anton-vinogradov/esp32-leshy2/drafts/legacy-2026-08-15/hardware/tscircuit/README.md

# Leshy2 — schematic as code (tscircuit)

The schematic sheets are captured as [tscircuit](https://tscircuit.com) code (`.tsx`)
transcribed from the transcribe-ready net-lists in [`hardware/`](../). From one
source file tscircuit generates the **schematic image**, a **PCB**, a **netlist**,
and a **KiCad export** — so nothing is drawn by hand.

## Sheets

| File | Sheet | Source doc |
|---|---|---|
| `power.tsx` | 1 · Power | [power.md](../power/power.md) |
| `c5-buses.tsx` | 2 · MCU + buses | [c5-buses.md](../c5-buses/c5-buses.md) |
| `rf.tsx` | 3 · RF chains | [rf.md](../rf/rf.md) |
| `audio.tsx` | 4 · Audio | [audio.md](../audio/audio.md) |
| `expansion.tsx` | 5 · Expansion (Grove-UART GPS port) | [expansion.md](../expansion/expansion.md) |
| `indicators.tsx` | 6 · Indicators / IO | [indicators.md](../indicators/indicators.md) |
| `integration.tsx` | board-level (display FPC · antenna u.FL · UI buttons · U14) | — merged, not a design sheet |

The six subsystem sheets — plus `integration.tsx` (the board-level parts that span
subsystems: the display FPC, the antenna u.FL array, the UI button block and its 3rd
PCA9555) — are **merged into one board** by `merge.py`; see below.

## Combined board — fab-drafted

All sheets are realized with **real parts**: every IC/module/connector pulls its
manufacturer-verified footprint + pinout from the LCSC/JLCPCB database
(`footprint="jlcpcb:C…"`); only mechanical/placeholder parts stay geometric.
**`board.tsx` is GENERATED** by [`merge.py`](merge.py): it strips each sheet's `<board>`
wrapper, renames the three cross-sheet refdes collisions (`U20`→`m_U20`/`rf_U20`,
`Y1`→`rf_Y1`/`a_Y1`, `Rbias`→`rf_Rbias`/`a_Rbias`), and concatenates the six sheets +
`integration.tsx` into one `<board>`. The sheets stitch by shared `net.NAME` (the whole
SPI/I²C bus, the power rails, the chip-selects, the interrupts, the C5 link, the SP4T
select). **223 components.** Never hand-edit `board.tsx` — edit a sheet (or
`integration.tsx`), then re-run `python3 merge.py`.

| File | What |
|---|---|
| `board.tsx` | **generated** — the whole device in one board (do **not** hand-edit) |
| `merge.py` | builds `board.tsx` from the 6 sheets + `integration.tsx` |
| `board-sch.svg` | whole-board schematic image |
| `board.kicad_pcb` | **KiCad PCB — the layout target (connectivity carried; not yet routed)** |

## Placement & auto-routing — drafted

From `board.kicad_pcb` an **auto-placement draft** groups the parts (a pre-integration 174-part draft) into floorplan
zones — RF up near the antenna edge, power at the bottom, MCU + buses in the centre —
with the cable/slot connectors pinned to their board edges (USB-C at the bottom,
microSD on the left, Grove on the right) and **zero courtyard overlaps**. It is
converted to a **4-layer** stack (JLC7628, `In1` = GND plane, `In2` + outer = signal)
with a real design-rule floor in the sibling `.kicad_pro`.

The digital + power nets are **auto-routed with [Freerouting](https://github.com/freerouting/freerouting)**
(board → Specctra DSN → freerouting → SES → back into KiCad via `pcbnew`), then the GND
pads are **welded to the `In1` plane** by [KiCadRoutingTools](https://github.com/drandyhaas/KiCadRoutingTools)'
plane-finalize. Result: **424 of 425 connections routed** on 4 layers — 3304 track
segments + 715 vias over a filled GND plane (0.003 Ω, ~15 A) — leaving only **one net
(the encoder B channel) + 4 DRC clearance nits**. The RF traces exist but still want an
impedance-controlled, coplanar-ground, antenna-keep-out **hand-redo in KiCad** (as RF
always does); finish those few touches → gerbers.

| File | What |
|---|---|
| `board-placed-4layer.kicad_pcb` | pre-route — 4-layer, edge-aware placement, GND-plane zone |
| `board-autorouted.kicad_pcb` | **Freerouting draft** — ~85 % routed, GND plane filled; hand-finish the rest |

> The placement is a **draft**: single-sided at ~80 × 175 mm to open routing channels;
> moving the small decoupling caps to the back shrinks it toward ~80 × 140 mm.
> Freerouting 2.x runs headless on Java 21+ (`-de in.dsn -do out.ses -mp N`); DSN/SES
> cross the KiCad boundary with `pcbnew.ExportSpecctraDSN` / `ImportSpecctraSES`.

## Render / export

Needs Node + [Bun](https://bun.sh) (the tscircuit CLI runs on Bun):

```bash
npm install                       # once — installs @tscircuit/cli locally (runs on Bun)
python3 merge.py                  # (re)generate board.tsx from the 6 sheets + integration.tsx
# Sheets use footprint="jlcpcb:C…" -> the parts engine (network) must be ON.
# Do NOT pass --disable-parts-engine, or the real footprints won't resolve.
# NOTE: give -o a RELATIVE path — the CLI mishandles a leading "/".
npx tsci export board.tsx -f kicad_pcb     -o board.kicad_pcb     # whole-board PCB (layout target)
npx tsci export board.tsx -f schematic-svg -o board-sch.svg      # whole-board schematic
# also: pcb-svg, gerbers, kicad_zip, readable-netlist, STEP, glTF …
```

**Verify connectivity** with KiCad's DRC. On the *un-placed / un-routed* merged board the
connectivity signal is **`schematic_parity` = 0** (the PCB netlist matches the schematic — no
accidental merges or breaks). Its `unconnected_items` (ratsnest) and `shorting_items` (pads of
different nets physically overlapping because nothing is placed yet) are **both artifacts of the
pre-layout board**, not real defects — they clear once parts are placed and routed:
`kicad-cli pcb drc --format json -o board.drc.json board.kicad_pcb`.

## Notes

- **Real footprints** are engine-pulled by LCSC part number (the parts engine /
  network must be on to export). Remaining **placeholders** to swap before fab: the
  18650 holder, 3.5 mm jack, electret mic, speaker, buzzer, RESET/BOOT/PTT buttons,
  the nRF24 / SA868 module lands and the CC1101 balun; LEDs are plain 0603 (pick the
  real amber part at BOM time). Each sheet's header comment lists its exact parts + `⚠`.
- **On the board now** (integration sheet): the display FPC (`J_LCD`, `LCD_*`), the
  CC1101 / UHF / Si4732 antenna u.FL connectors (`J_ANT_*`, `ANT_*`), the UI button
  block (D-pad + BACK/OPTIONS/STOP/F1/F2) and its 3rd PCA9555 (`U14`, 0x22).
- **Still off-sheet before the PCB** — intentional dangling endpoints today:
  the 7 RF envelope detectors that feed the TX-live LEDs (`TXDET_*`, Stage 3),
  the C5 USB VBUS ESD stub (`VBUS_C5`), and the module-level antennas that live on
  their own modules (the 3 nRF24 lands, the LoRa E22 IPEX).
- **RF PCB layout** (impedance-controlled feeds, ground planes, antenna
  keep-outs) is done in **KiCad** on the exported project — the auto-router is
  not used for the RF chains.
- Connectivity is by **net name** (`net.BAT`, `net.GND`, …), matching the
  "Key nets" sections of each sheet doc.
- **Schematic of record = the `.tsx` + `*-schematic.svg`** (connectivity is
  correct there). tscircuit's `kicad_sch` export currently drops the wires
  (dangling labels — fails KiCad ERC), so it is **not** committed; the
  KiCad **`.kicad_pcb`** carries the real net connectivity and is the layout
  target.

*Part of [Leshy2](../../README.md) · MIT.*
