anton-vinogradov/esp32-leshy2/drafts/project-history-2026-08-19/review/baseline.md

# Baseline перестройки документации

Дата фиксации: 2026-08-15, Europe/Moscow.

| Репозиторий | Исходный commit | Состояние до переноса |
|---|---|---|
| `esp32-leshy2` | `355ac489ba995614695874d40474fb845e7944d1` | актуальный `origin/main` перед reset |
| `esp32-leshy2-firmware` | `28e7c46710f00ab179df1b0eb488616da173688c` | актуальный `origin/main` перед reset |

Старая документация перенесена в `drafts/legacy-2026-08-15/` внутри каждого репозитория. Она сохраняет исследовательскую ценность и историю решений, но больше не является источником требований.

Старый `docsync` также архивирован: его контрольные хэши и ссылки были привязаны к прежней структуре. Новый контроль согласованности будет введён после появления первых проверенных контрактов.
