anton-vinogradov/esp32-leshy2/drafts/project-history-2026-08-19/review/reviews/REV-0005CE-current-g3-clamshell-propagation.md

# REV-0005CE — current G3 clamshell propagation

Статус: **проведено ревью geometry-reentry working projection**.

| Проверка | Результат |
|---|---|
| process entry | pass: I1…I9 working-candidate paper scopes reviewed before integrated mockup resumed |
| legacy reuse | pass: fold/mirror, board envelope, holes, inner gap and geometric checks reused without inheriting old owner/device labels |
| current locality | pass: S3+C5 UI/control half and RP RF/power half preserve electrical owners while keeping active local interfaces local |
| external inventory | pass: 3.5-inch HMX, all controls, three USB roles, storage/audio/IR, nine SMA identities, U214, Unit and exact battery family remain visible |
| drawing semantics | pass: one numbered body per shown physical device; exact/current MPN and role in one register; dashed power region is not a device |
| physical checks | pass: board bounds/overlap, SMA spacing/hole clearance, U214 overhang/gaps and complete control/antenna identity checks |
| hardware regression | pass: generator/artifact checks, 73 architecture/product tests and whitespace check |
| firmware regression | pass: 19 runtime/landing tests |
| authorization boundary | pass: G3 continues; G4 alternatives, G5 selection, G6 co-design, G7 atomic architecture and KiCad remain later gates |

## Verdict

[`G3-0001`](../product-design/G3-0001-current-clamshell-reentry.md) receives
**«Проведено ревью»** for geometry re-entry. [`FND-0117`](../findings/FND-0117-legacy-layout-was-not-a-current-g3-projection.md)
is fixed. The generated view is the current starting physical hypothesis, not
the finished product design.

Next G3 work expands the placement-critical envelope and connector/cable plane;
any physical conflict returns to its G2F owner. KiCad remains unauthorized.
