anton-vinogradov/esp32-leshy2/drafts/project-history-2026-08-19/review/reviews/REV-0005BP-bounded-principled-and-stage-diagrams.md

# REV-0005BP — bounded principled and current-stage diagrams

Статус: **проведено ревью документационных диаграмм**.

| Проверка | Результат |
|---|---|
| reproduced failure | pass: monolithic landing-page Mermaid source exceeded the GitHub text limit |
| rendered boundary | pass: first target diagram is vertical and below 12,000 source characters |
| physical identity | pass: every overview box contains one physical component, its MPN and role |
| no data loss | pass: exhaustive one-device-per-node raw projection and exact pin/net tables remain machine-generated/reviewable |
| current position | pass: gate diagram distinguishes internal `I8` inside `2F` from future top-level gate `8` |
| architecture delta | none: no component, instance, owner, pin, signal, rail or BOM quantity changed |
| regression | pass: 69/69 architecture tests, generated-artifact check and whitespace check |

## Verdict

[`FND-0113`](../findings/FND-0113-monolithic-principled-diagram-exceeded-github-limit.md)
is corrected. The start pages again provide a useful finished-product diagram,
while the exhaustive projection stays available without asking GitHub to render
an unsupported monolith.

`FND-0114/REV-0005BZ` later supersede the hidden-source presentation with a
rendered split atlas and replace the USB-led overview with owner-first maps.
The original electrical/architecture verdict remains unchanged.

I8 remains active. I9, integrated mockup and KiCad remain unauthorized.
