anton-vinogradov/esp32-leshy2/drafts/project-history-2026-08-19/review/reviews/REV-0005BZ-renderable-principled-atlas.md

# REV-0005BZ — renderable principled-device atlas

Статус: **проведено ревью документационных диаграмм**.

| Проверка | Результат |
|---|---|
| landing-page entry | pass: architecture starts from S3/C5/RP ownership, not USB |
| readable slices | pass: separate S3, C5, RP and power diagrams in both target README files |
| exhaustive projection | pass: all 858 current physical instances are emitted; 44 PD/charger support positions missing from the old raw view were restored |
| Mermaid boundary | pass: 25 detailed blocks; largest block remains below the 12,000-character limit |
| physical identity | pass: one physical instance per node with exact/current MPN and role; explicit `MPN TBD` remains visible |
| raw preservation | pass: full monolithic `.mmd` is generated as a machine-review artifact |
| synchronization | pass: generator rewrites and checks both target README sections together with the detailed atlas |
| architecture delta | none: no device, quantity, owner, pin, signal, rail, power policy or BOM value changed |
| regression | pass: generated-artifact check, architecture suite and whitespace check |

## Verdict

[`FND-0114`](../findings/FND-0114-hidden-projection-and-usb-led-overview.md)
получает статус **«Исправлено»**. Диаграммный шаг получает статус
**«Проведено ревью»**: landing page объясняет архитектуру от владельцев, а
полная начинка действительно рендерится несколькими ограниченными схемами.

I8, I9, integrated mockup и KiCad не продвигаются этим документационным
изменением.
