anton-vinogradov/esp32-leshy2/drafts/project-history-2026-08-19/review/reviews/REV-0004L-digital-noninterference-layout.md

# REV-0004L — digital non-interference layout

> Subsequent amendment: `DEC-0059/REV-0005L` replaces the reviewed 4-bit
> S3↔C5 pin group with dedicated 1-bit SDIO plus full S3/C5 service. Current
> machine evidence is in `NIF-0001` and the generated atlas.

- Статус: **Проведено ревью исходной компоновки; current budget повторно проверен `REV-0004V`**
- Дата: 2026-08-17
- Decision: [`DEC-0044`](../decisions/DEC-0044-delegated-noninterference-layout.md)
- Artifact: [`NIF-0001`](../architecture/NIF-0001-digital-noninterference-layout.md)
- Machine source: [`G2F-3I`](../../../hardware/architecture/candidates/G2F-3I.json)

## Проверки

| Проверка | Результат |
|---|---|
| exact S3/C5 module and RP2354B QFN80 contacts exist | pass |
| every programmable exposed GPIO is used/reserved/free exactly once | current pass after `DEC-0046`: S3 `29/3/4`, C5 `14/6/1`, RP `48/0/0`; corrected by `FND-0059/REV-0004V` |
| every TCA6424 allocatable contact classified | historical pass: `23/1/0`; subsequent audio/CC reviews produced main `23/0/1`; post-DEC-0098 current projection is main `24/0/0` plus UI `7/1/0` |
| duplicate JSON keys fail before semantic validation | pass |
| every strap allocation has explicit reset proof | pass |
| every programmable peer link reciprocates the same net | pass |
| each domain has independent programming/recovery/diagnostics | pass on contacts: S3 USB, C5 UART0+EN/BOOT/strap, RP USB+SWD+RUN+BOOTSEL |
| RP2354B PIO data pins obey the real shared base window | pass: PIO0 and PIO1 select `GPIO16…GPIO47`; all PIO data are `GPIO30…GPIO46` |
| fixed-function mux contacts match exact-device groups | pass: S3 USB, C5 4-bit SDIO, RP SPI1/UART0/UART1/I²C0 contracts |
| RP PIO state-machine capacity | pass: `5/12`, seven reserve |
| RP DMA worst-case persistent capacity | pass: `13/16`, three reserve |
| S3 directional GDMA capacity | pass: TX `3/5`, RX `3/5`; two reserve in each direction |
| 3×nRF24, CC1101 and U214 share a data bus | no; five physical buses/state machines |
| C5 IPC shares controller with microSD | no; C5 exclusively uses S3 SD/MMC host |
| RP IPC shares controller with display/storage | no; dedicated SPI3/SPI1 |
| remaining scheduled resources declare arbiter/deadline/proof gate | pass: display+SD and internal slow I²C only |
| generator tests | historical pass: 19 tests; current suite is rerun and reported by the newest review artifact |

## Найдено и исправлено в ходе перебора

| Несоответствие | Исправление |
|---|---|
| RP2354A forced four compatibility radios onto one 10 Mbit/s bus | RP2354B/QFN80 and four independent PIO0 buses |
| first B-package map put C5 and microSD on one S3 host | microSD moved to SPI2; C5 gets exclusive 4-bit SDIO |
| proposed RP UART gave only 1.6 MB/s raw against ≥1.5 MB/s framed gate | rejected; RP returns to dedicated 20 MHz SPI |
| proposed C5 UART ignored exact 5 Mbit/s device limit | rejected using official ESP-IDF SoC capability |
| first RP2354B pin map crossed the physical PIO GPIO-base window | all five PIO data groups moved into `GPIO16…GPIO47`; CS/CE/IRQ remain direct GPIO; machine regression added |
| 16-port slow plane did not cover 19…27 demand | accepted 24-port envelope; 23 endpoints routed, one reserve |
| old validator could not detect duplicate JSON keys or service alternatives | parser/validator and regression tests extended |
| post-review quiet-state controls made the displayed C5/RP budget stale | counts regenerated and protected by focused pinout artifact/test in `FND-0059/REV-0004V` |

## Review boundary

Статус относится к **бумажной цифровой компоновке и её machine checks**, а не
к complete target architecture. Physical RF coexistence, electrical signal
integrity, exact peripheral MPNs, power, mechanics, cost and HIL remain open.
Следующий шаг — RF self-desense/coexistence proof; неизбежную взаимную
деградацию нельзя закрыть этим ревью.
