anton-vinogradov/esp32-leshy2/drafts/project-history-2026-08-19/review/reviews/REV-0005AO-display-endpoint-propagation.md

# REV-0005AO — display endpoint propagation review

> Subsequent `REV-0005AQ` changes TP_INT routing and consumes GPIO39/47 for the
> encoder; the display endpoint reviewed here otherwise remains unchanged.

- Status: **Проведено ревью**
- Decision: [`DEC-0084`](../decisions/DEC-0084-exact-protected-display-electrical-endpoint.md)
- Finding: [`FND-0088`](../findings/FND-0088-display-endpoint-still-contained-abstract-circuits.md)

## Propagation checked

| Consumer | Result |
|---|---|
| machine device registry | exact connector, switch and two new resistor MPNs expose every real contact |
| G2F-3I instances/routes | connector separates board and panel; logic/backlight/reset/fault routes are exact; no GPIO added |
| allocation regression | S3 remains `32 used / 3 reserved / 1 free`; GPIO40 now ends on the exact PWM gate circuit |
| product diagram | every added physical component is a separate vertical-diagram node with MPN and role |
| display register/fit docs | prior exact 40-contact fit is amended by the protected electrical endpoint while procurement/mate evidence stays open |
| firmware contract | reset waits, default-off backlight, latch behavior, no auto-retry and HIL-only connector maturity are explicit |
| stage state | I4 remains active; only the display paper electrical endpoint receives «Проведено ревью» |

## Review boundary

The checked JSON and generated atlas agree, and the paper circuit has no
abstract display supply/backlight endpoint. This review does not authorize
KiCad, connector footprint freeze, panel purchase as a production MPN or any
mechanical mockup update.
