anton-vinogradov/esp32-leshy2/drafts/project-history-2026-08-19/review/reviews/REV-0005V-2s-manager-decision-propagation.md

# REV-0005V — 2S manager decision propagation

- Статус: **Проведено ревью**
- Дата: 2026-08-18
- Decision: [`DEC-0066`](../decisions/DEC-0066-max17320-mspm0-fail-closed-manager.md)
- Device review: [`PWR-0005`](../architecture/PWR-0005-replaceable-2s-manager-options.md)

## Review result

| Check | Result |
|---|---|
| owner choice | pass: option A accepted exactly as `MAX17320G20+T + MSPM0C1104SDGS20R` |
| real devices | pass: current ADI/TI order codes, lifecycle, package and all exposed contacts are machine-recorded |
| no hidden authentication | pass: exact G20 has no SHA-256; no secret or irreversible lock is required |
| startup safety | pass at architecture level: protected gauge image/readback is a production interlock; ALRT hold remains asserted across blank/reset/watchdog admission MCU states |
| service/recovery | pass at boundary: gauge I2C/NVM/hold/fault and MCU NRST/SWD/UART/VDD/VSS have direct fixture access |
| MCU GPIO budget | pass: 10 used, 5 reserved, 3 free across all 18 real DGS20 GPIO-capable contacts |
| MCU power claim | pass with explicit boundary: AOLDO is only for measured low-clock operation; programming/recovery uses an isolated external source |
| system integration | pass: dedicated local gauge bus; bounded shared system I2C/IRQ; no radio/display/storage controller dependency |
| target diagrams | pass: EN/RU and generated vertical diagrams show the two exact physical devices separately with roles |
| firmware projection | pass: local admission ownership and fourth independently recoverable image domain are propagated; S3 cannot override refusal |
| downstream electrical work | open but bounded: exact FET/fuse/NTC/shunt/load/hold/supply-isolation and HIL are named |
| CAD boundary | pass: no KiCad authorization implied |

## Conclusion

The exact manager decision, contacts, resources, recovery and cross-repository
projection receive **«Проведено ревью»**. `I3` advances to the complete
MAX17320 surrounding circuit and loss/fault calculations.
