anton-vinogradov/esp32-leshy2/drafts/project-history-2026-08-19/review/improvements/IMP-0053-5v-typec-versus-pd-charge-path.md

# IMP-0053 — 5-V Type-C power path versus USB-PD

- Статус: **Принято B; закрыто DEC-0063/REV-0005R**
- Дата: 2026-08-18
- Context: [`PWR-0003`](../architecture/PWR-0003-charge-power-path-options.md)
- Battery behavior: [`DEC-0062`](../decisions/DEC-0062-individually-replaceable-2s-cells.md)
- Decision: [`DEC-0063`](../decisions/DEC-0063-sink-only-30w-usb-pd-power-path.md)

## Decision options

- **A / `C5V` — recommended:** ordinary 5-V Type-C/legacy input with explicit
  source-current detection, 2S NVDC boost charger/power path and separate real
  gauge/protector. Lowest complete BOM and complexity; charging is load-aware
  and may slow/pause during high-power use.
- **B / `CPD`:** USB-C PD controller plus wide-input 1–4S buck-boost charger.
  Faster/more headroom, but adds cost, area, PD image/provisioning, compliance
  and high-voltage fault work without a current product requirement.
- **C / `CLEG`:** repair the old BQ25887 design with external missing blocks.
  Rejected as dominated after its apparent part-count advantage disappears.

## Historical recommendation and owner decision

Accept **A / C5V**. It preserves ordinary charger compatibility, USB-only
recovery and battery supplement without paying for unrequested fast charging.

After the owner requested the installed-cost delta, the complete comparison
showed approximately USD 2–3/device at the visible 100-piece tier rather than
an order-of-magnitude penalty. The owner explicitly selected **B / CPD** and
bounded it to sink-only 30 W. `DEC-0063/PWR-0004` supersede the historical
recommendation and add the mandatory EEPROM/provisioning/recovery details.
