anton-vinogradov/esp32-leshy2/drafts/project-history-2026-08-19/review/reviews/REV-0005N-target-product-site-cleanup.md

# REV-0005N — target product-site cleanup

- Статус: **Проведено ревью**
- Дата: 2026-08-17
- Decision: [`DEC-0060`](../decisions/DEC-0060-github-target-product-site.md)
- Finding: [`FND-0072`](../findings/FND-0072-target-readmes-contained-engineering-chronology.md)

## Проверено

| Проверка | Результат |
|---|---|
| hardware EN/RU landing | product purpose, capabilities, physical design, safety and docs navigation retained |
| firmware EN/RU landing | product behavior, UI, radio services, data, STOP, update/recovery and docs navigation retained |
| review chronology | `DEC/REV/FND/IMP` chains removed from all four target pages |
| maturity | detailed progress remains in both `docs/status/current-state.*.md` pairs |
| traceability | review ledger and current-state links remain visible at top/bottom |
| hardware diagram | vertical `flowchart TD`, exact MPN coverage and one-device-per-node projection retained |
| pin mapping | exact groups retained in responsive `<details>` list; generated atlas remains linked |
| firmware visualization | vertical safe-session state flow added in both languages |
| product scope | no accepted capability, exclusion or safety guarantee removed |
| regression | hardware architecture suite **41/41 pass**; firmware target-page suite **2/2 pass** |

## Boundary

Этот review подтверждает качество entrypoints и сохранение принятого product
scope. Он не повышает зрелость electronics/firmware implementation и не закрывает
никакие текущие component, power, RF, HIL или `INT-0001/I2` decisions.
