anton-vinogradov/esp32-leshy2/drafts/project-history-2026-08-19/review/reviews/REV-0005J-internals-before-integrated-mockup.md

# REV-0005J — internals before integrated mockup propagation review

- Статус: **Проведено ревью процесса; subsequent `DEC-0059/REV-0005L` закрывают I1 и активируют I2**
- Дата: 2026-08-17
- Decision: [`DEC-0058`](../decisions/DEC-0058-internals-before-integrated-mockup.md)
- Sequence: [`INT-0001`](../architecture/INT-0001-internal-design-closure-sequence.md)

## Проверенный результат

| Gate | Результат |
|---|---|
| owner instruction | pass: integrated mockup resumes only after internal-design closure |
| existing U214 proof | retained: `PHY-0001/DEC-0057` remains a bounded envelope decision, not continued industrial design |
| process cycle | pass: project-level electrical closure is separated from prototype/enclosure-only HIL |
| physical work boundary | pass: local part/connector/thermal/RF fit checks remain allowed only as internal feasibility inputs |
| dependency order | pass: `INT-0001/I0…I9` covers compute, safety, power, UI, audio, RF, expansion, BOM and whole-internal review |
| next prerequisite | pass: compute/recovery/service is first; `FND-0070/IMP-0049` exposes rather than hides the SDIO collision |
| target behavior | no delta: product capability and three safety levels do not change |
| firmware repository | historical at this review; `DEC-0059` later creates the transport delta |

## Conclusion

The previous wording that the next pass starts integrated G3 mockup is
superseded. Current work stays in internal feasibility/closure until `I9`;
mockup and industrial layout remain paused, while KiCad is still blocked.
