anton-vinogradov/esp32-leshy2/drafts/project-history-2026-08-19/review/audits/AUD-0004-current-competitor-capability-gap.md

# AUD-0004 — current competitor capability and product-design gap

- Статус: **Проведено ревью; `W-EXTRA-11..17` закрыты**
- Дата snapshot: 2026-08-16
- Finding: [`FND-0040`](../findings/FND-0040-current-competitor-benchmark-missing.md)
- Scope: official product/project documentation; shipping and prototype states
  are never merged

## Representative products

| Product/class | Current official facts relevant to Leshy2 | Design lesson, not copied solution |
|---|---|---|
| Flipper Zero, shipping compact multi-tool | 100×40×25 mm, 102 g, 2100 mAh, 1.4-inch sunlight-readable 128×64 LCD, D-pad/back, microSD, USB-C, CC1101, LF RFID, NFC, IR, BLE/802.15.4, iButton and GPIO; claimed battery life up to 28 days | pocket control can remain complete without touch/keyboard; field runtime/readability, lanyard and contact tools are product-level requirements |
| M5 Cardputer-Adv, shipping card terminal | 84×54×19.6 mm, 81 g, 1750 mAh, 56-key keyboard, 240×135 display, ES8311/mic/speaker/jack, IR TX, microSD, Grove and 14-pin expansion, lanyard; U214 Cap adds LoRa+GNSS | keyboard and cap mechanics are viable in a small device, but screen area and antenna/accessory volume are constrained |
| LILYGO T-Deck Plus, shipping dev platform | 100×68×11 mm, 2.8-inch 320×240, keyboard+trackball, 2000 mAh, microSD, LoRa and GNSS; no touch; Plus consumes its Grove pins for GNSS | large landscape face improves UI/text, while fixed onboard radios can remove general expansion and force bus sharing |
| LILYGO T-Embed CC1101, shipping integrated dev platform | 97.5×39×31 mm, 1.9-inch 320×170, encoder, CC1101, PN532, IR, mic/speaker, TF, 1300 mAh and two QWIIC ports | narrow one-hand/encoder shell can carry many blocks, but thickness, controls and RF/antenna honesty need explicit review |
| ESP32 Marauder, active open project | hardware variants deliberately span 2.8-inch touch, 1.44-inch 5-way compact control, SD/battery/GPS and CLI; current feature matrix includes Wi-Fi/BLE analysis, raw capture and PMKID | one firmware does not prove one optimal enclosure; control/display profiles are real product variants |
| Flipper One, **prototype not for sale** | preliminary 155×67×40 mm, 22.9 Wh, Linux RK3576 + low-power RP2350, 256×144 grayscale display, D-pad/touchpad/PTT, USB host/PD, Wi-Fi 6E 2.4/5/6, M.2 and modular antenna rail | high-speed/Linux/extensible class is physically and economically different; its provisional features are competitor direction, not a baseline fact to clone |
| HackRF One, shipping SDR peripheral | open 1 MHz–6 GHz half-duplex, 20 Msps 8-bit IQ, high-speed USB, no autonomous UI/battery | wideband SDR requires a different RF/compute/data/power class; external/deferred disposition is honest unless the whole product class changes |

## Sources

- [Flipper Zero official product/specifications](https://flipper.net/)
- [Flipper Zero iButton](https://docs.flipper.net/zero/ibutton) and
  [U2F](https://docs.flipper.net/zero/u2f) documentation
- [Flipper One preliminary technical specifications](https://docs.flipper.net/one/general/tech-specs),
  [Wi-Fi/Bluetooth](https://docs.flipper.net/one/hardware/wifi-bluetooth) and
  [module mounting](https://docs.flipper.net/one/mechanics/module-mounting-system)
- [M5Stack Cardputer-Adv](https://docs.m5stack.com/en/core/Cardputer-Adv) and
  [Cardputer Mesh Kit/U214](https://docs.m5stack.com/en/core/Cardputer_Mesh_Kit)
- [LILYGO T-Deck Plus](https://wiki.lilygo.cc/products/t-deck-series/t-deck-plus/)
- [LILYGO T-Embed CC1101](https://wiki.lilygo.cc/products/t-embed-series/t-embed-cc1101/)
- [ESP32 Marauder current hardware matrix](https://github.com/justcallmekoko/ESP32Marauder/wiki/marauder-versions)
- [Great Scott Gadgets HackRF One](https://greatscottgadgets.com/hackrf/one/)
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
