anton-vinogradov/esp32-leshy2/drafts/project-history-2026-08-19/review/decisions/DEC-0058-internals-before-integrated-mockup.md

# DEC-0058 — finish the internal design before resuming the integrated mockup

- Статус: **Принято владельцем; проведено ревью propagation**
- Дата: 2026-08-17
- Основание: прямое указание владельца продолжать mockup только после полного
  завершения работ над начинкой
- Closure sequence: [`INT-0001`](../architecture/INT-0001-internal-design-closure-sequence.md)
- Review: [`REV-0005J`](../reviews/REV-0005J-internals-before-integrated-mockup.md)
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
