anton-vinogradov/esp32-leshy2/hardware/product-design/g3_clamshell.py

#!/usr/bin/env python3
"""Generate and validate dimensioned Leshy2 mechanical projections."""

from __future__ import annotations

import argparse
import html
import json
import math
import xml.etree.ElementTree as ET
from dataclasses import dataclass
from pathlib import Path


REPO = Path(__file__).resolve().parents[2]
DEVICES_PATH = REPO / "hardware/architecture/devices.json"
CANDIDATE_PATH = REPO / "hardware/architecture/candidates/G2F-3I.json"
MECHANICAL_GATES_PATH = REPO / "hardware/product-design/mechanical-evidence-gates.json"
SOURCE_RESEARCH_PATH = REPO / "hardware/product-design/h1-source-research.json"
NAVIGATION_CLUSTER_PATH = REPO / "hardware/product-design/navigation-cluster.json"
DISPLAY_MOUNT_DESIGN_PATH = REPO / "hardware/product-design/display-mount.json"
ASSEMBLY_COORDINATE_MODEL_PATH = REPO / "hardware/product-design/assembly-coordinate-model.json"
H1_R2_PLACEMENT_PATH = REPO / "hardware/product-design/h1-r2-placement.json"
EXTERNAL_OUTPUT = REPO / "docs/images/current-clamshell.svg"
SERVICE_OUTPUT = REPO / "docs/images/service-access.svg"
INTERNAL_OUTPUT = REPO / "docs/images/internal-board-layout.svg"
SANDWICH_OUTPUT = REPO / "docs/images/sandwich-section.svg"
TOP_EDGE_OUTPUT = REPO / "docs/images/top-edge-view.svg"
NAVIGATION_OUTPUT = REPO / "docs/images/navigation-cluster.svg"
DISPLAY_MOUNT_OUTPUT = REPO / "docs/images/display-mount.svg"
SOURCE_TABLE_OUTPUT = REPO / "hardware/product-design/generated/H1-physical-source-table.json"
SOURCE_REGISTER_OUTPUT = REPO / "docs/physical-source-register.md"
UNIFIED_COORDINATE_TABLE_OUTPUT = REPO / "hardware/product-design/generated/H1-unified-coordinate-table.json"
EXTERNAL_ACCEPTANCE_OUTPUT = REPO / "hardware/product-design/generated/H1-external-face-acceptance.json"
CROSS_VIEW_ACCEPTANCE_OUTPUT = REPO / "hardware/product-design/generated/H1-cross-view-acceptance.json"

BOARD_W = 80.0
BOARD_H = 150.0
DISPLAY_Y = 10.5
DISPLAY_W = 56.54
DISPLAY_H = 84.96
DISPLAY_X = (BOARD_W - DISPLAY_W) / 2
MOUNT_HOLE_D = 2.7
MOUNT_KEEPOUT_R = 4.0
HOLES = ((5.0, 11.0), (BOARD_W - 5.0, 11.0), (5.0, 145.0), (BOARD_W - 5.0, 145.0))

INTERBOARD_GAP_MM = 11.0
MIN_INTERBOARD_Z_CLEARANCE_MM = 0.7
INTENTIONAL_INTERBOARD_MATES = {
    ("m1_ui_plug", "m1_rf_receptacle"),
}

U214_X = (BOARD_W - 84.0) / 2
U214_Y = 17.02
U214_W = 84.0
U214_H = 24.0
U214_CLEARANCE = 0.7
U214_CONNECTOR_W = 17.78
U214_CONNECTOR_D = 5.08
U214_CONNECTOR_PTH_KEEPOUT_W = 17.78
U214_CONNECTOR_PTH_KEEPOUT_D = 3.81
U214_CONNECTOR_X = (BOARD_W - U214_CONNECTOR_W) / 2
# The U214 male Cap-Bus exits normal to its broad rear face.  The exact host
# socket is therefore vertical on the raised Cardputer-like rear rail and is
# projected beneath the installed Cap envelope, not beside it.
U214_CONNECTOR_Y = U214_Y + (U214_H - U214_CONNECTOR_D) / 2
U214_RETENTION_PITCH = 56.0
U214_RETENTION_X = (
    U214_X + (U214_W - U214_RETENTION_PITCH) / 2,
    U214_X + (U214_W + U214_RETENTION_PITCH) / 2,
)
U214_RETENTION_Y = U214_Y + U214_H / 2
PACK_HOLDER_Y = 42.0
PACK_HOLDER_H = 86.0
PACK_CELL_Y = PACK_HOLDER_Y + 10.0
PACK_HOLDER_BODY_W = 39.78
PACK_HOLDER_BODY_H = 77.06
PACK_HOLDER_X_OFFSET = 0.0
PACK_HOLDER_CENTRE_X = BOARD_W / 2
PACK_HOLDER_PAD_X = PACK_HOLDER_CENTRE_X - 39.8 / 2
PACK_HOLDER_DRAWING_X = PACK_HOLDER_PAD_X
PACK_HOLDER_BODY_X = PACK_HOLDER_CENTRE_X - PACK_HOLDER_BODY_W / 2
PACK_CELL_CENTRES_X = (PACK_HOLDER_CENTRE_X - 9.55, PACK_HOLDER_CENTRE_X + 9.55)
PACK_HOLDER_BODY_Y = PACK_HOLDER_Y + (PACK_HOLDER_H - PACK_HOLDER_BODY_H) / 2

# Exact GCT RFPC-SMA31/SMA32 1.6-mm edge-launch family. The 10.2-mm
# plan width includes the nut envelope; the 6-mm board-side depth comes from
# the exact land/body drawing rather than the full external threaded length.
RF_BODY_W = 10.2
RF_BODY_D = 6.0
RF_BARREL_D = 6.35
RF_BARREL_OUT = 11.4
FRONT_RF = (
    (10.6, "N24-0", "SMA"),
    (25.3, "S3-2G4", "RP-SMA"),
    (40.0, "N24-1", "SMA"),
    (54.7, "C5-2G4/5", "RP-SMA"),
    (69.4, "N24-2", "SMA"),
)
REAR_RF = (
    # Five 10.2-mm SMA bodies use equal 14.7-mm pitch.
    (10.6, "RX-FM/SW", "SMA"),
    (25.3, "RX-AM/LW", "SMA"),
    (40.0, "CC-SUB", "SMA"),
    (54.7, "VOICE-VHF", "SMA"),
    (69.4, "VOICE-UHF", "SMA"),
)
VOICE_V_RF_CORRIDOR = ((54.7, 0.0), (20.25, 32.52))
VOICE_U_RF_CORRIDOR = (
    (69.4, 0.0),
    (69.4, 6.0),
    (66.5, 6.0),
    (66.5, 30.0),
    (71.2, 36.95),
)
OPPOSITE_FACE_CLEARANCE_MM = 1.5

# H1-R2.39 fail-closed placement scope. These are the already accepted G2F-3I
# Cap-Bus protection/control and hardware TX-evidence aggregate bodies. The
# values bind each instance to its current exact device key: a substitution,
# omitted coordinate or duplicate projection must fail generation.
CAP_EVIDENCE_COORDINATE_INSTANCE_DEVICES = {
    "u214_connector": "samtec_hle_107_02_g_dv_pe_lc",
    "u214_i2c_iso": "tca4307dgkr",
    "u214_i2c_iso_bypass": "yageo_cc0402krx7r9bb104",
    "u214_i2c_host_sda_pullup": "uniroyal_0402wgf2201tce",
    "u214_i2c_host_scl_pullup": "uniroyal_0402wgf2201tce",
    "u214_host_buffer_a": "nexperia_74lvc126apw_118",
    "u214_host_buffer_b": "nexperia_74lvc126apw_118",
    "u214_return_buffer": "nexperia_74lvc126apw_118",
    "u214_host_buffer_a_bypass": "yageo_cc0402krx7r9bb104",
    "u214_host_buffer_b_bypass": "yageo_cc0402krx7r9bb104",
    "u214_return_buffer_bypass": "yageo_cc0402krx7r9bb104",
    "u214_series_rst": "panasonic_erj_2rkf22r0x",
    "u214_series_gps_rx": "panasonic_erj_2rkf22r0x",
    "u214_series_sck": "panasonic_erj_2rkf22r0x",
    "u214_series_mosi": "panasonic_erj_2rkf22r0x",
    "u214_series_nss": "panasonic_erj_2rkf22r0x",
    "u214_series_busy": "panasonic_erj_2rkf22r0x",
    "u214_series_irq": "panasonic_erj_2rkf22r0x",
    "u214_series_gps_tx": "panasonic_erj_2rkf22r0x",
    "u214_series_miso": "panasonic_erj_2rkf22r0x",
    "u214_esd_a": "ti_tpd4e05u06_dqar",
    "u214_esd_b": "ti_tpd4e05u06_dqar",
    "u214_esd_c": "ti_tpd4e05u06_dqar",
    "u214_req_pulldown": "yageo_rc0402fr_0710kl",
    "u214_supervisor": "ti_tps3808g33_dbvr",
    "u214_supervisor_bypass": "yageo_cc0402krx7r9bb104",
    "u214_supervisor_sense_top": "yageo_rc0402fr_07110kl",
    "u214_supervisor_sense_bottom": "yageo_rc0402fr_07220kl",
    "u214_supervisor_ct": "murata_grm155r71h103ka88d",
    "u214_supervisor_pullup": "yageo_rc0402fr_0710kl",
    "any_tx_aon_pullup": "yageo_rc0402fr_0710kl",
    "evidence_or_0": "onsemi_bat54alt1g",
    "evidence_or_1": "onsemi_bat54alt1g",
    "evidence_or_2": "onsemi_bat54alt1g",
    "evidence_or_3": "onsemi_bat54alt1g",
    "evidence_or_4": "onsemi_bat54alt1g",
    "evidence_main_isolator": "ti_sn74lvc3g07_dcur",
    "evidence_main_isolator_bypass": "yageo_cc0402krx7r9bb104",
    "ext_evidence_buffer": "ti_sn74lvc1g07_dckr",
    "ext_evidence_buffer_bypass": "yageo_cc0402krx7r9bb104",
    "ext_evidence_input_pullup": "yageo_rc0402fr_0710kl",
    "ext_evidence_input_series": "yageo_rc0402fr_071kl",
    "ext_evidence_output_pullup": "yageo_rc0402fr_0710kl",
}
CAP_EVIDENCE_COURTYARD_HALO_MM = 0.35
RF_INSTANCE_BY_PATH = {
    "S3-2G4": "s3_external_rp_sma",
    "C5-2G4/5": "c5_external_rp_sma",
    "RX-FM/SW": "receiver_fmsw_external_sma",
    "RX-AM/LW": "receiver_amlw_external_sma",
    "N24-0": "nrf0_external_sma",
    "CC-SUB": "cc_external_sma",
    "N24-1": "nrf1_external_sma",
    "VOICE-VHF": "voice_v_external_sma",
    "VOICE-UHF": "voice_external_sma",
    "N24-2": "nrf2_external_sma",
}
RF_SOURCE_INSTANCE_BY_PATH = {
    "S3-2G4": "s3",
    "C5-2G4/5": "c5",
    "RX-FM/SW": "receiver",
    "RX-AM/LW": "receiver",
    "N24-0": "nrf0",
    "CC-SUB": "cc",
    "N24-1": "nrf1",
    "VOICE-VHF": "voice_v",
    "VOICE-UHF": "voice",
    "N24-2": "nrf2",
}
BOARD_RF_CABLE_TO_TRACE_HANDOFFS = frozenset(
    {
        "s3_rf_board_connector",
        "c5_rf_board_connector",
        "nrf0_rf_board_connector",
        "nrf1_rf_board_connector",
        "nrf2_rf_board_connector",
    }
)
RF_USER_LABEL_LINES = {
    "S3-2G4": ("WI-FI/BLE", "2.4 GHz"),
    "C5-2G4/5": ("WI-FI/15.4", "2.4/5 GHz"),
    "RX-FM/SW": ("FM/SW", "AIR RX"),
    "RX-AM/LW": ("AM/LW LOOP",),
    "N24-0": ("nRF1", "2.4 GHz"),
    "CC-SUB": ("SUB-GHz",),
    "N24-1": ("nRF2", "2.4 GHz"),
    "VOICE-VHF": ("VHF", "VOICE", "134-174"),
    "VOICE-UHF": ("UHF", "VOICE", "400-480"),
    "N24-2": ("nRF3", "2.4 GHz"),
}
# Optional per-path label coordinates for derivative layouts.  Coordinates
# are PCB millimetres in the matching outer-face frame.  Keeping them in the
# drawing input lets the geometry audit reject silk hidden by a connector,
# cable, display, Cap or mounting keep-out instead of relying on hand tuning.
RF_COMPACT_LABEL_POSITIONS = {
    "N24-0": (14.8, 7.8),
    "N24-2": (65.2, 7.8),
    "RX-FM/SW": (18.0, 7.8),
    "VOICE-UHF": (64.0, 7.8),
}
TX_RF_PATHS = {
    "S3-2G4", "C5-2G4/5", "N24-0", "CC-SUB", "N24-1", "VOICE-VHF", "VOICE-UHF", "N24-2"
}
TX_LED_W = 1.6
TX_LED_H = 0.8
TX_LED_INSTANCES = {
    "S3-2G4": "s3_tx_led",
    "C5-2G4/5": "c5_tx_led",
    "N24-0": "nrf0_tx_led",
    "CC-SUB": "cc_tx_led",
    "N24-1": "nrf1_tx_led",
    "VOICE-VHF": "voice_tx_led",
    "VOICE-UHF": "voice_tx_led",
    "N24-2": "nrf2_tx_led",
}
FRONT_FACE_INDICATORS = (
    ("s3_tx_led", "WI-FI/BLE", 7.6, 104.5),
    ("c5_tx_led", "WI-FI/15.4", 23.4, 104.5),
    ("nrf0_tx_led", "nRF24-1", 39.2, 104.5),
    ("nrf1_tx_led", "nRF24-2", 55.0, 104.5),
    ("nrf2_tx_led", "nRF24-3", 70.8, 104.5),
    ("cc_tx_led", "SUB-GHz", 7.6, 111.0),
    ("voice_tx_led", "V/U TX", 23.4, 111.0),
    ("ir_tx_led", "IR", 39.2, 111.0),
    ("ext_tx_led", "LORA/EXT", 55.0, 111.0),
    ("fault_led", "FAULT", 70.8, 111.0),
)
PROJECT_REPOSITORY_URL = "github.com/anton-vinogradov/esp32-leshy2"
OUTER_FACE_PRODUCT_MARKS = (
    ("front", "Леший", BOARD_W / 2, 99.5, 10.5),
    ("rear", "ESP32-LESHY2", BOARD_W / 2, 136.0, 7.5),
    ("rear", PROJECT_REPOSITORY_URL, BOARD_W / 2, 142.0, 5.0),
)

# Every directional interface that crosses the enclosure is rendered here.
# `coordinate` is Y for left/right exits and X for bottom exits.
EDGE_INTERFACES = (
    ("ir_demod", "front", "left", 76.5, "IR 38 kHz RX"),
    ("ir_carrier", "front", "left", 83.5, "IR raw RX"),
    ("ir_emitter", "front", "left", 90.255, "IR TX"),
    ("headphone_jack", "front", "right", 79.75, "HEADSET / CTIA"),
    ("c5_service_usb_connector", "front", "bottom", 31.47, "C5 SERVICE USB"),
    ("sd", "front", "bottom", 55.975, "microSD"),
    ("power_command_switch", "rear", "right", 112.75, "RUN / KILL"),
    ("product_usb_connector", "rear", "bottom", 16.47, "USB / POWER"),
    ("rp_service_usb_connector", "rear", "bottom", 37.47, "RP SERVICE USB"),
    ("microphone", "front", "bottom", 47.0, "MICROPHONE"),
    ("unit_connector", "rear", "bottom", 57.0, "M5 UNIT"),
    ("s3_reset_button", "front", "left", 117.25, "S3 RST"),
    ("s3_boot_button", "front", "left", 124.25, "S3 BOOT"),
    ("c5_reset_button", "front", "right", 117.25, "C5 RST"),
    ("c5_boot_button", "front", "right", 124.25, "C5 BOOT"),
    ("rp_reset_button", "rear", "left", 108.25, "RP RST"),
    ("rp_boot_button", "rear", "left", 115.25, "RP BOOT"),
)

EXTERNAL_SERVICE_BUTTONS = frozenset(
    {
        "s3_reset_button", "s3_boot_button",
        "c5_reset_button", "c5_boot_button",
        "rp_reset_button", "rp_boot_button",
    }
)
SERVICE_BUTTON_RECESS_MM = 1.2

# Internal acoustic components can require an exterior label without inventing
# enclosure-slot geometry on the PCB-face projection.
EXTERNAL_COMPONENT_LABELS = (
    ("speaker", "rear", "right", 133.0, "SPEAKER"),
)

# External side projections show only real silkscreen labels and an enclosure
# direction arrow.  They must not invent a visible button/socket body on the
# face, and the front labels must fit wholly in the two gutters beside the
# display envelope.
SIDE_INTERFACE_LABEL_LINES = {
    "ir_demod": ("IR 38 kHz RX",),
    "ir_carrier": ("IR RAW RX",),
    "ir_emitter": ("IR TX",),
    "headphone_jack": ("HEADSET", "CTIA"),
    "power_command_switch": ("RUN", "KILL"),
    "s3_reset_button": ("S3 RST",),
    "s3_boot_button": ("S3 BOOT",),
    "c5_reset_button": ("C5 RST",),
    "c5_boot_button": ("C5 BOOT",),
    "rp_reset_button": ("RP RST",),
    "rp_boot_button": ("RP BOOT",),
}


@dataclass(frozen=True)
class Placement:
    instance: str
    x: float
    y: float
    role: str
    rotation: int = 0


@dataclass(frozen=True)
class CableRoute:
    instance: str
    points: tuple[tuple[float, float], ...]
    role: str


@dataclass(frozen=True)
class CableReserve:
    """Conservative cable space when the exact module connector axis is H5 evidence."""

    instance: str
    module_instance: str
    board_connector_instance: str
    escape_points: tuple[tuple[float, float], ...]
    role: str


@dataclass(frozen=True)
class ThroughBoardFeature:
    """One pin/tab envelope that protrudes from an outer-face part into the gap."""

    assembly_instance: str
    feature: str
    x: float
    y: float
    w: float
    h: float
    inner_height: float
    role: str


@dataclass(frozen=True)
class AntennaTopologyGuide:
    """One visible source-to-antenna relation; never a claim of routed copper."""

    instance: str
    path: str
    frame: str
    source_instance: str
    external_instance: str
    points: tuple[tuple[float, float], ...]
    role: str


@dataclass(frozen=True)
class BodyProjectionContract:
    """Mechanical meaning of one rendered body outside the placement maps."""

    instance: str
    frame: str
    rotation: int
    direction: str


@dataclass(frozen=True)
class Reserve:
    name: str
    x: float
    y: float
    w: float
    h: float
    role: str
    reserve_class: str


UI_INNER = (
    Placement("s3_rf_coupler", 15.2, 6.2, "S3 forward-power coupler beside the outward RP-SMA"),
    Placement("c5_rf_coupler", 63.2, 6.2, "C5 dual-band forward-power coupler beside the outward RP-SMA"),
    Placement("s3_rf_board_connector", 14.5, 9.0, "S3 30-mm jumper board receptacle"),
    Placement("c5_rf_board_connector", 62.5, 9.0, "C5 30-mm jumper board receptacle"),
    Placement("s3", 5.3, 22.0, "UI, display, storage and audio owner; shifted 0.7 mm outward for the central display ZIF corridor"),
    Placement("c5", 56.7, 22.0, "native 2.4/5-GHz and IR owner; shifted into the widened right routing field"),
    Placement("display_connector", 26.5, 25.0, "direct 50-contact dual-contact ZIF behind the folded display FPC slot; connector pin 1 at world x-max, tail pin 1 mates connector pin 50 at world x-min"),
    Placement("slow_io", 24.0, 55.0, "24-line slow-control expander"),
    Placement("ui_matrix_io", 33.0, 55.0, "sixteen-line direct-control input expander"),
    Placement("codec", 42.0, 55.0, "audio capture and playback codec"),
    Placement("audio_speaker_selector", 42.0, 62.0, "active differential speaker-path selector"),
    Placement("receiver", 51.0, 54.0, "FM/AM/SW/LW receiver"),
    Placement("ir_demod", 0.0, 75.0, "38-kHz IR receiver"),
    Placement("ir_carrier", 0.0, 82.0, "carrier-learning IR receiver"),
    Placement("ir_emitter", 0.0, 89.0, "940-nm IR transmitter"),
    Placement("ir_safe_gate", 8.0, 75.0, "UI-local FAULT_KILL-qualified IR carrier gate"),
    Placement("evidence_cmp_a", 8.0, 82.0, "UI-local S3/C5/IR TX evidence comparator"),
    Placement("ui_zone_ntc", 12.0, 75.0, "UI/display hotspot safety sensor"),
    Placement("codec_i2s_din_boot_gate", 18.0, 75.0, "CODEC_READY and AUDIO_ARM gate protecting S3 boot GPIO0"),
    Placement("safe_reset_sink_a", 18.0, 82.0, "UI-local S3/C5 passive-drain reset sinks"),
    Placement("safe_c5_reset_buffer", 22.0, 82.0, "UI-local RUN_PERMIT C5 reset inverter"),
    Placement("safe_c5_fault_reset_buffer", 25.0, 82.0, "UI-local direct FAULT_ASSERT_N C5 reset sink"),
    Placement("headphone_jack", 65.4, 76.0, "3.5-mm CTIA headset TRRS mid-mount connector"),
    Placement("headset_control_io", 54.2, 77.0, "dedicated 0x39 headset source controller and seven reserve I/O lines"),
    Placement("m1_ui_plug", 22.2, 119.0, "80-contact M1 plug; 11-mm board stack"),
    Placement("c5_service_usb_connector", 27.0, 142.65, "C5 data-only service USB"),
    Placement("sd", 48.0, 136.15, "bottom-access push-push microSD", 90),
    Placement("s3_dbg_header", 5.0, 104.0, "keyed S3 UART0/RESET/BOOT header"),
    Placement("s3_reset_button", 0.0, 115.0, "external left-side S3 RESET service control", 90),
    Placement("s3_boot_button", 0.0, 122.0, "external left-side S3 BOOT service control", 90),
    Placement("c5_dbg_header", 47.0, 104.0, "keyed C5 UART0/RESET/BOOT header"),
    Placement("c5_reset_button", 76.6, 115.0, "external right-side C5 RESET service control", 270),
    Placement("c5_boot_button", 76.6, 122.0, "external right-side C5 BOOT service control", 270),
)

# Exact module-side axes come from the Espressif package drawings. The visible
# line is only the direct 2D projection between connector axes: a flexible
# cable has no PCB-like orthogonal route. The selected assembly is 30 mm long;
# its remaining 3D slack, bend radius and retention close on the H5 coupon.
UI_RF_CABLES = (
    CableRoute(
        "s3_rf_jumper",
        ((20.3, 24.46), (16.0, 10.55)),
        "direct S3 U.FL-to-U.FL plan projection; 30-mm assembly slack closes at H5",
    ),
    CableRoute(
        "c5_rf_jumper",
        ((71.7, 24.38), (64.0, 10.55)),
        "direct C5 U.FL-to-U.FL plan projection; 30-mm assembly slack closes at H5",
    ),
)

# These are topology guides, not routed copper. They connect all ten radio
# sources to the matching outward antenna datum. S3/C5 and nRF guides continue
# after the visible microcoax at the board-mounted U.FL; the four direct paths
# begin at the receiver, CC1101 or SA818S source. KiCad owns final geometry.
ANTENNA_TOPOLOGY_GUIDES = (
    AntennaTopologyGuide(
        "s3_native_rf_pcb_guide",
        "S3-2G4",
        "ui-inner",
        "s3_rf_board_connector",
        "s3_external_rp_sma",
        ((16.0, 10.55), (25.3, 6.62), (25.3, 0.0)),
        "S3 board U.FL through forward coupler to outward S3 RP-SMA",
    ),
    AntennaTopologyGuide(
        "c5_native_rf_pcb_guide",
        "C5-2G4/5",
        "ui-inner",
        "c5_rf_board_connector",
        "c5_external_rp_sma",
        ((64.0, 10.55), (54.7, 6.62), (54.7, 0.0)),
        "C5 board U.FL through forward coupler to outward C5 RP-SMA",
    ),
    AntennaTopologyGuide(
        "receiver_fmsw_pcb_guide",
        "RX-FM/SW",
        "ui-inner",
        "receiver",
        "receiver_fmsw_external_sma",
        ((51.0, 54.8), (16.0, 49.0), (16.0, 6.0), (10.6, 6.0), (10.6, 0.0)),
        "Si4732 FMI matching and protection to outward FM/SW SMA",
    ),
    AntennaTopologyGuide(
        "receiver_amlw_pcb_guide",
        "RX-AM/LW",
        "ui-inner",
        "receiver",
        "receiver_amlw_external_sma",
        ((51.0, 56.2), (25.3, 52.0), (25.3, 0.0)),
        "Si4732 AMI coupling and protection to outward AM/LW SMA",
    ),
    AntennaTopologyGuide(
        "nrf0_pcb_guide",
        "N24-0",
        "rf-inner",
        "nrf0_rf_board_connector",
        "nrf0_external_sma",
        ((24.5, 29.55), (12.0, 29.55), (12.0, 5.0), (10.6, 5.0), (10.6, 0.0)),
        "nRF24 #0 board U.FL through forward coupler to outward SMA",
    ),
    AntennaTopologyGuide(
        "nrf1_pcb_guide",
        "N24-1",
        "rf-inner",
        "nrf1_rf_board_connector",
        "nrf1_external_sma",
        ((56.5, 29.55), (56.75, 27.0), (56.75, 5.0), (40.0, 5.0), (40.0, 0.0)),
        "nRF24 #1 board U.FL through forward coupler to outward SMA",
    ),
    AntennaTopologyGuide(
        "nrf2_pcb_guide",
        "N24-2",
        "rf-inner",
        "nrf2_rf_board_connector",
        "nrf2_external_sma",
        ((76.5, 23.55), (70.2, 27.5), (70.2, 5.0), (69.4, 5.0), (69.4, 0.0)),
        "nRF24 #2 board U.FL through forward coupler to outward SMA",
    ),
    AntennaTopologyGuide(
        "cc_sub_pcb_guide",
        "CC-SUB",
        "rf-inner",
        "cc",
        "cc_external_sma",
        ((24.0, 10.3), (40.0, 5.0), (40.0, 0.0)),
        "CC1101 selected matching branch to outward Sub-GHz SMA",
    ),
    AntennaTopologyGuide(
        "voice_v_pcb_guide",
        "VOICE-VHF",
        "rf-inner",
        "voice_v",
        "voice_v_external_sma",
        tuple(reversed(VOICE_V_RF_CORRIDOR)),
        "SA818S-V contact 12 to outward VHF 134-174-MHz SMA",
    ),
    AntennaTopologyGuide(
        "voice_u_pcb_guide",
        "VOICE-UHF",
        "rf-inner",
        "voice",
        "voice_external_sma",
        tuple(reversed(VOICE_U_RF_CORRIDOR)),
        "SA818S-U contact 12 to outward UHF 400-480-MHz SMA",
    ),
)

RF_INNER = (
    Placement("nrf0_rf_board_connector", 23.0, 28.0, "nRF24 #0 Gen1 jumper board receptacle"),
    Placement("nrf1_rf_board_connector", 52.9, 28.0, "nRF24 #1 Gen1 jumper board receptacle"),
    Placement("nrf2_rf_board_connector", 75.0, 22.0, "nRF24 #2 Gen1 jumper board receptacle"),
    Placement("rp", 0.0, 32.2, "deterministic radio owner"),
    Placement("nrf0", 9.0, 7.5, "full-function nRF24 radio #0"),
    Placement("nrf1", 39.5, 7.5, "full-function nRF24 radio #1; clear of the CC reference zone and U214 socket tails"),
    Placement("nrf2", 54.9, 7.5, "full-function nRF24 radio #2; clear of the top-right mounting keep-out"),
    Placement("voice_v", 15.8, 32.52, "VHF 134-174-MHz SA818S-V; dedicated contact-12 RF path", 180),
    Placement("voice", 52.2, 32.5, "UHF 400-480-MHz SA818S-U; dedicated contact-12 RF path", 270),
    Placement("cc", 30.0, 8.3, "multi-band sub-GHz transceiver inside its local reference RF zone"),
    Placement("nvdc_charger", 1.0, 63.0, "2S charger and NVDC power path"),
    Placement("pack_gauge", 1.0, 84.0, "2S protection and fuel gauge"),
    Placement("pack_admission", 5.7, 84.0, "fail-closed battery admission MCU"),
    Placement("aon_buck", 43.0, 61.0, "always-on 3.3-V converter"),
    Placement("main_buck", 20.0, 61.0, "main 3.3-V converter"),
    Placement("voice_buck", 28.0, 61.0, "voice 4.0-V converter"),
    Placement("ext_buck", 36.0, 61.0, "accessory 5.0-V converter"),
    Placement("power_zone_ntc", 25.5, 84.0, "power-conversion hotspot safety sensor"),
    Placement("rf_zone_ntc", 72.0, 56.0, "RF/voice hotspot safety sensor"),
    Placement("safety_controller", 36.0, 87.0, "independent watchdog, thermal and TX-lease controller"),
    Placement("safety_watchdog", 37.0, 94.0, "independent 1.6-s timeout watchdog"),
    Placement("safe_conditioner", 42.0, 94.0, "RUN and S3 fault-reset conditioner"),
    Placement("safe_latch", 37.0, 82.0, "asynchronous RUN_PERMIT / FAULT_KILL latch"),
    Placement("safe_reset_buffer", 41.0, 82.0, "C5/RP fault-reset buffer"),
    Placement("safe_fault_reset_buffer", 44.5, 85.0, "direct FAULT_ASSERT_N C5/RP reset and voice eFuse clamp"),
    Placement("safe_rearm_buffer", 44.0, 82.0, "delayed physical re-arm Schmitt buffer"),
    Placement("safe_supervisor", 49.0, 82.0, "always-on safety supervisor"),
    Placement("safe_reset_sink_b", 55.0, 82.0, "RP reset sink"),
    Placement("safe_ptt_or", 59.0, 82.0, "FAULT_KILL-dominant voice PTT gate"),
    Placement("safe_gate_b", 49.0, 88.0, "rear-domain transmit safety gates"),
    Placement("cc_backup_gate", 57.0, 100.0, "independent FAULT_ASSERT_N CC1101 rail qualifier"),
    Placement("evidence_cmp_b", 58.0, 88.0, "RF-local nRF/CC TX evidence comparator"),
    Placement("evidence_cmp_voice", 66.0, 88.0, "RF-local voice TX evidence comparator"),
    Placement("product_usb_protector", 7.5, 135.0, "product USB CC/USB2 protector"),
    Placement("pd_controller", 11.5, 134.5, "sink-only USB-PD controller"),
    Placement("speaker_amp", 31.0, 87.0, "rear-local differential speaker amplifier"),
    Placement("safe_gate_a", 49.0, 94.0, "nRF-domain transmit safety gates"),
    Placement("nrf_backup_gate", 54.0, 100.0, "independent FAULT_ASSERT_N nRF rail qualifier"),
    Placement("m1_rf_receptacle", 22.2, 119.0, "80-contact M1 receptacle; 11-mm board stack"),
    Placement("product_usb_connector", 12.0, 143.1, "product USB-C data and sink"),
    Placement("rp_service_usb_connector", 33.0, 142.65, "RP data-only service USB"),
    Placement("unit_connector", 51.0, 140.9, "native M5 Unit HY2.0-4P edge receptacle"),
    Placement("microphone", 45.0, 146.0, "rear bottom-facing microphone"),
    Placement("speaker", 50.0, 127.0, "internal 4-Ohm differential speaker"),
    Placement("rp_dbg_header", 40.0, 104.0, "keyed RP SWD/RUN/USB_BOOT header"),
    Placement("rp_reset_button", 0.0, 106.0, "external left-side RP RUN/RESET service control", 90),
    Placement("rp_boot_button", 0.0, 113.0, "external left-side RP USB_BOOT service control", 90),
    Placement("power_command_switch", 70.8, 111.0, "single low-current RUN/KILL; charging remains available in KILL"),

    Placement("voice_band_io", 44.0, 68.8, "TCA9534A UHF/VHF selector and deterministic reset straps"),
    Placement("voice_control_mux_a", 49.7, 68.8, "selected-module UART multiplexer"),
    Placement("voice_control_mux_b", 53.55, 68.8, "selected-module PTT and AUDIO_ON multiplexer"),
    Placement("voice_audio_mux", 44.0, 74.55, "selected-module AFOUT and microphone multiplexer", 90),
    Placement("voice_band_inverter", 49.75, 74.55, "AON complement for one-hot voice selection; TSOP6 rotated for local clearance", 90),
    Placement("voice_pd_gate", 52.45, 74.55, "AON mutually-exclusive voice PD gate"),
    Placement("u214_host_buffer_a", 16.0, 52.55, "U214 host-command buffer A"),
    Placement("u214_host_buffer_b", 21.8, 52.55, "U214 host-command buffer B"),
    Placement("u214_return_buffer", 27.6, 52.55, "U214 return-path buffer"),
    Placement("u214_i2c_iso", 33.45, 52.55, "U214 hot-swap I2C isolation and stuck-bus recovery"),
    # Canonical support-body pack. These are H1 body/courtyard coordinates;
    # H2 still owns trace order and the connector-side ESD launch constraint.
    Placement("u214_supervisor", 72.0, 57.5, "U214 3V3_OUT admission supervisor"),
    Placement("u214_esd_a", 32.0, 58.5, "U214 connector-side ESD array A"),
    Placement("u214_esd_b", 43.0, 58.0, "U214 connector-side ESD array B"),
    Placement("u214_esd_c", 28.5, 58.0, "U214 connector-side ESD array C"),
    Placement("u214_i2c_iso_bypass", 33.5, 60.5, "U214 I2C isolator local bypass"),
    Placement("u214_i2c_host_sda_pullup", 31.5, 60.5, "U214 host-side SDA pull-up"),
    Placement("u214_i2c_host_scl_pullup", 49.0, 52.5, "U214 host-side SCL pull-up"),
    Placement("u214_host_buffer_a_bypass", 49.0, 54.0, "U214 host-buffer A bypass"),
    Placement("u214_host_buffer_b_bypass", 26.5, 58.0, "U214 host-buffer B bypass"),
    Placement("u214_return_buffer_bypass", 46.5, 58.0, "U214 return-buffer bypass"),
    Placement("u214_series_rst", 49.0, 55.5, "U214 RST 22-ohm source series"),
    Placement("u214_series_gps_rx", 26.5, 59.5, "U214 GPS_RX 22-ohm source series"),
    Placement("u214_series_sck", 24.5, 58.0, "U214 SCK 22-ohm source series"),
    Placement("u214_series_mosi", 45.5, 60.0, "U214 MOSI 22-ohm source series"),
    Placement("u214_series_nss", 49.0, 57.0, "U214 NSS 22-ohm source series"),
    Placement("u214_series_busy", 24.5, 59.5, "U214 BUSY 22-ohm source series"),
    Placement("u214_series_irq", 47.5, 59.5, "U214 IRQ 22-ohm source series"),
    Placement("u214_series_gps_tx", 22.5, 58.0, "U214 GPS_TX 22-ohm source series"),
    Placement("u214_series_miso", 49.5, 58.5, "U214 MISO 22-ohm source series"),
    Placement("u214_req_pulldown", 22.5, 59.5, "U214 request-line fail-safe pull-down"),
    Placement("u214_supervisor_bypass", 72.0, 59.9, "U214 supervisor local bypass"),
    Placement("u214_supervisor_sense_top", 72.0, 61.2, "U214 supervisor upper sense leg"),
    Placement("u214_supervisor_sense_bottom", 72.0, 62.5, "U214 supervisor lower sense leg"),
    Placement("u214_supervisor_ct", 72.0, 63.8, "U214 supervisor delay capacitor"),
    Placement("u214_supervisor_pullup", 72.0, 65.1, "U214 supervisor output pull-up"),
    Placement("nrf0_host_buffer", 0.0, 26.8, "nRF24 #0 host-command buffer"),
    Placement("nrf0_return_buffer", 6.0, 26.8, "nRF24 #0 return-path buffer"),
    Placement("nrf1_host_buffer", 37.3, 52.55, "nRF24 #1 host-command buffer"),
    Placement("nrf1_return_buffer", 39.25, 58.0, "nRF24 #1 return-path buffer"),
    Placement("nrf2_host_buffer", 43.1, 52.55, "nRF24 #2 host-command buffer"),
    Placement("nrf2_return_buffer", 55.65, 74.55, "nRF24 #2 return-path buffer"),
    Placement("cc_host_buffer", 57.4, 68.8, "CC1101 host-command buffer"),
    Placement("cc_return_buffer", 63.2, 68.8, "CC1101 return-path buffer"),
    Placement("cc_band_buffer", 59.4, 74.55, "CC1101 band-select buffer"),

    # High-profile and high-current support parts are explicit physical bodies,
    # not hidden inside a generic power-zone rectangle.
    Placement("charger_inductor", 6.0, 62.4, "BQ25798 2.2-uH switching inductor"),
    Placement("charger_vbus_cap0", 1.0, 69.0, "BQ25798 VBUS bulk capacitor #0"),
    Placement("charger_vbus_cap1", 4.9, 69.0, "BQ25798 VBUS bulk capacitor #1"),
    Placement("charger_pmid_cap0", 8.8, 69.0, "BQ25798 PMID bulk capacitor #0"),
    Placement("charger_pmid_cap1", 12.7, 69.0, "BQ25798 PMID bulk capacitor #1"),
    Placement("charger_pmid_cap2", 1.0, 71.3, "BQ25798 PMID bulk capacitor #2"),
    Placement("charger_sys_cap0", 4.9, 71.3, "BQ25798 SYS bulk capacitor #0"),
    Placement("charger_sys_cap1", 8.8, 71.3, "BQ25798 SYS bulk capacitor #1"),
    Placement("charger_sys_cap2", 12.7, 71.3, "BQ25798 SYS bulk capacitor #2"),
    Placement("charger_sys_cap3", 1.0, 73.6, "BQ25798 SYS bulk capacitor #3"),
    Placement("charger_sys_cap4", 4.9, 73.6, "BQ25798 SYS bulk capacitor #4"),
    Placement("charger_bat_cap0", 8.8, 73.6, "BQ25798 BAT bulk capacitor #0"),
    Placement("charger_bat_cap1", 12.7, 73.6, "BQ25798 BAT bulk capacitor #1"),
    Placement("charger_regn_cap", 1.0, 75.9, "BQ25798 REGN local capacitor"),

    Placement("main_inductor", 19.0, 64.0, "main 3.3-V 3.3-uH switching inductor"),
    Placement("main_input_cap", 19.0, 70.0, "main 3.3-V input bulk capacitor"),
    Placement("main_output_cap0", 22.9, 70.0, "main 3.3-V output bulk capacitor #0"),
    Placement("main_output_cap1", 19.0, 73.2, "main 3.3-V output bulk capacitor #1"),
    Placement("voice_inductor", 27.0, 64.0, "voice 4.0-V 3.3-uH switching inductor"),
    Placement("voice_input_cap", 27.0, 70.0, "voice 4.0-V input bulk capacitor"),
    Placement("voice_output_cap0", 30.9, 70.0, "voice 4.0-V output bulk capacitor #0"),
    Placement("voice_output_cap1", 27.0, 73.2, "voice 4.0-V output bulk capacitor #1"),
    Placement("ext_inductor", 35.0, 64.0, "accessory 5.0-V 4.7-uH switching inductor"),
    Placement("ext_buck_input_cap", 35.0, 70.0, "accessory 5.0-V input bulk capacitor"),
    Placement("ext_buck_output_cap0", 39.0, 70.0, "accessory 5.0-V output bulk capacitor #0"),
    Placement("ext_buck_output_cap1", 35.0, 73.2, "accessory 5.0-V output bulk capacitor #1"),
    Placement("aon_inductor", 46.0, 64.0, "always-on 3.3-V 2.2-uH switching inductor"),
    Placement("aon_input_cap", 42.0, 64.0, "always-on 3.3-V input capacitor"),
    Placement("aon_output_cap", 42.0, 66.3, "always-on 3.3-V output capacitor"),

    Placement("pack_fuse0", 1.0, 80.0, "protected-pack branch fuse #0"),
    Placement("pack_fuse1", 7.8, 80.0, "protected-pack branch fuse #1"),
    Placement("pack_shunt", 14.6, 80.0, "Kelvin pack-current shunt"),
    Placement("pack_power_fet", 21.7, 80.0, "back-to-back pack admission FET"),
    Placement("pack_diag_res0", 11.5, 84.0, "pack diagnostic pulse resistor #0"),
    Placement("pack_diag_res1", 18.5, 84.0, "pack diagnostic pulse resistor #1"),
    Placement("evidence_mask", 63.15, 74.55, "AON evidence-source mask expander"),
    # Firmware-independent rear-domain evidence OR aggregate.
    Placement("evidence_or_2", 58.0, 86.0, "evidence diode OR for nRF24 #2 / CC"),
    Placement("any_tx_aon_pullup", 56.0, 90.5, "AON pull-up for hardware ANY_TX aggregate"),
    Placement("evidence_or_3", 64.0, 91.5, "evidence diode OR for voice / IR"),
    Placement("ext_evidence_buffer", 55.0, 92.0, "5-V-tolerant U214 pin-5 evidence boundary"),
    Placement("evidence_main_isolator", 58.0, 93.5, "AON-to-main hardware evidence isolator"),
    Placement("evidence_or_1", 62.0, 93.5, "evidence diode OR for nRF24 #0 / #1"),
    Placement("evidence_main_isolator_bypass", 56.0, 94.0, "main evidence-isolator bypass"),
    Placement("evidence_or_4", 62.0, 95.5, "evidence diode OR for external Cap evidence"),
    Placement("evidence_or_0", 58.0, 96.5, "evidence diode OR for S3 / C5"),
    Placement("ext_evidence_buffer_bypass", 56.0, 89.0, "U214 evidence-buffer local bypass"),
    Placement("ext_evidence_input_pullup", 56.0, 95.5, "U214 pin-5 fail-safe input pull-up"),
    Placement("ext_evidence_input_series", 56.0, 87.5, "U214 pin-5 evidence input series resistor"),
    Placement("ext_evidence_output_pullup", 58.0, 98.5, "isolated U214 evidence output pull-up"),

    Placement("pd_pphv_cap0", 1.0, 127.0, "USB-PD high-voltage bulk capacitor #0"),
    Placement("pd_pphv_cap1", 4.9, 127.0, "USB-PD high-voltage bulk capacitor #1"),
    Placement("pd_pphv_cap2", 8.8, 127.0, "USB-PD high-voltage bulk capacitor #2"),
    Placement("pd_pphv_cap3", 12.7, 127.0, "USB-PD high-voltage bulk capacitor #3"),
    Placement("pd_config_eeprom", 16.3, 134.5, "TPS25751 configuration EEPROM"),
    Placement("pd_vbus_cap", 22.0, 134.5, "raw VBUS local capacitor"),
    Placement("pd_vbus_tvs", 26.0, 134.5, "raw VBUS flat-clamp TVS"),
)

# Ebyte publishes the module and land-pattern envelope but not the current-lot
# Gen1 receptacle axis.  The complete module face therefore remains a legal
# cable-head zone; only the short escape to the exact board receptacle is fixed.
# Cable slack stays above that face, while bend/retention closes on the H5 coupon.
RF_NRF_CABLE_RESERVES = (
    CableReserve(
        "nrf0_rf_jumper",
        "nrf0",
        "nrf0_rf_board_connector",
        ((22.0, 25.6), (24.5, 29.55)),
        "direct nRF24 #0 IPEX-zone-to-board-U.FL projection; module axis closes at H5",
    ),
    CableReserve(
        "nrf1_rf_jumper",
        "nrf1",
        "nrf1_rf_board_connector",
        ((39.5, 20.0), (54.4, 29.55)),
        "direct nRF24 #1 IPEX-zone-to-board-U.FL projection; module axis closes at H5",
    ),
    CableReserve(
        "nrf2_rf_jumper",
        "nrf2",
        "nrf2_rf_board_connector",
        ((69.5, 23.55), (76.5, 23.55)),
        "direct nRF24 #2 IPEX-zone-to-board-U.FL projection; module axis closes at H5",
    ),
)

SIDE_FUNCTION_CONTROLS = (
    Placement("ui_switch_f1", 1.8, 19.5, "front-left function F1"),
    Placement("ui_switch_f2", 1.8, 33.0, "front-left function F2"),
    Placement("ui_switch_f3", 1.8, 46.5, "front-left function F3"),
    Placement("ui_switch_f4", 1.8, 60.0, "front-left function F4"),
    Placement("ui_switch_f5", 71.6, 19.5, "front-right function F5"),
    Placement("ui_switch_f6", 71.6, 33.0, "front-right function F6"),
    Placement("ui_switch_f7", 71.6, 46.5, "front-right function F7"),
    Placement("ui_switch_f8", 71.6, 60.0, "front-right function F8"),
)

BOTTOM_NAV_CONTROLS = (
    Placement("ui_switch_back", 11.0, 129.4, "direct-press BACK"),
    Placement("ui_dpad_up", 36.7, 120.4, "direct-press navigation UP"),
    Placement("ui_dpad_down", 36.7, 138.4, "direct-press navigation DOWN"),
    Placement("ui_dpad_left", 27.7, 129.4, "direct-press navigation LEFT"),
    Placement("ui_dpad_right", 45.7, 129.4, "direct-press navigation RIGHT"),
    Placement("ui_dpad_ok", 36.7, 129.4, "direct-press navigation OK"),
    Placement("ui_switch_opt", 62.4, 129.4, "direct-press OPT"),
)

FRONT_CONTROLS = SIDE_FUNCTION_CONTROLS + BOTTOM_NAV_CONTROLS

DIRECT_PRESS_FRONT_CONTROLS = {item.instance for item in FRONT_CONTROLS}

REAR_CONTROLS = (
    Placement("encoder", 2.15, 44.5, "rear through-hole encoder"),
    Placement("ptt_switch", 69.2, 63.5, "rear independent PTT"),
)

DIRECT_PRESS_REAR_CONTROLS = {"ptt_switch"}

FRONT_CAP_RESERVES = ()

REAR_CAP_RESERVES = ()
REAR_CAP_TO_CONTROL = {}

REAR_SELECTED_ACTUATORS = (
    Placement("encoder_knob", 0.5, 43.0, "exact soft-touch knob over rear encoder"),
)

INTERNAL_RESERVES = (
    Reserve(
        "cc-reference-rf-network",
        29.3,
        7.5,
        9.5,
        17.5,
        "CC1101 broadband balun, switched band matching, detector tap and ESD zone",
        "selected_support_placement_zone",
    ),
)
INTERNAL_ZONE_ALLOWED_INSTANCES = {
    "cc-reference-rf-network": {"cc"},
}

# Bodies that are mechanically accounted for by a dedicated assembly or
# exterior projection rather than by one of the two inner-face placement maps.
MECHANICAL_ASSEMBLY_EMBEDDED_INSTANCES = {"display_touch_controller"}
MECHANICAL_EXTERIOR_INSTANCES = {
    "display", "u214", "pack_holder", "pack_cell0", "pack_cell1",
    *RF_INSTANCE_BY_PATH.values(),
    *(instance for instance, _, _, _ in FRONT_FACE_INDICATORS),
    *(route.instance for route in UI_RF_CABLES),
    *(reserve.instance for reserve in RF_NRF_CABLE_RESERVES),
}

REAR_OUTER = (
    Placement(
        "u214_connector",
        U214_CONNECTOR_X,
        U214_CONNECTOR_Y,
        "vertical host socket on the raised rear Cap-Bus rail",
    ),
)

# H1.1.2 source-normalisation contract. Placement coordinates always use the
# top-left of the rotated, axis-aligned manufacturer envelope. Rotations are
# clockwise in the named view. Each PCB face is authored as seen from its own
# exterior, so the rear board is mirrored only when it is transformed into the
# front-board datum for interboard collision checks.
MECHANICAL_PROJECTION_FRAMES = {
    "ui-inner": "UI PCB top-left, viewed from the front/exterior",
    "rf-inner": "RF/power PCB top-left, viewed from the rear/exterior",
    "front-outer": "UI PCB top-left, viewed from the front/exterior",
    "rear-outer": "RF/power PCB top-left, viewed from the rear/exterior",
    "ui-inner-route": "UI PCB top-left, viewed from the front/exterior",
    "rf-inner-route": "RF/power PCB top-left, viewed from the rear/exterior",
    "display-assembly": "ER-TFT035IPS-6 + ER-TPC035-6 configured CTP-outline top-left, front view",
}

PLACEMENT_PROJECTION_GROUPS = (
    ("ui-inner", UI_INNER),
    ("rf-inner", RF_INNER),
    ("front-outer", FRONT_CONTROLS),
    ("rear-outer", REAR_CONTROLS),
    ("rear-outer", REAR_OUTER),
    ("rear-outer", REAR_SELECTED_ACTUATORS),
)

INTERNAL_CONNECTOR_ACTUATOR_DIRECTIONS = {
    "display_connector": "horizontal FPC insertion toward the antenna edge; dual-contact ZIF; latch remains accessible after opening",
    "s3_rf_board_connector": "normal to the UI-inner face toward the cable plug",
    "c5_rf_board_connector": "normal to the UI-inner face toward the cable plug",
    "nrf0_rf_board_connector": "normal to the RF-inner face toward the Gen1 cable plug",
    "nrf1_rf_board_connector": "normal to the RF-inner face toward the Gen1 cable plug",
    "nrf2_rf_board_connector": "normal to the RF-inner face toward the Gen1 cable plug",
    "m1_ui_plug": "normal to the UI-inner face toward the RF/power board",
    "m1_rf_receptacle": "normal to the RF-inner face toward the UI board",
    "s3_dbg_header": "normal to the UI-inner face; enclosure-open service only",
    "c5_dbg_header": "normal to the UI-inner face; enclosure-open service only",
    "rp_dbg_header": "normal to the RF-inner face; enclosure-open service only",
    "s3_reset_button": "parallel to the UI PCB toward the left enclosure side; externally operable",
    "s3_boot_button": "parallel to the UI PCB toward the left enclosure side; externally operable",
    "c5_reset_button": "parallel to the UI PCB toward the right enclosure side; externally operable",
    "c5_boot_button": "parallel to the UI PCB toward the right enclosure side; externally operable",
    "rp_reset_button": "parallel to the RF PCB toward the left enclosure side; externally operable",
    "rp_boot_button": "parallel to the RF PCB toward the left enclosure side; externally operable",
    "nrf0": "normal to the RF-inner face inside the bounded module-face Gen1 endpoint zone; exact axis remains H5 evidence",
    "nrf1": "normal to the RF-inner face inside the bounded module-face Gen1 endpoint zone; exact axis remains H5 evidence",
    "nrf2": "normal to the RF-inner face inside the bounded module-face Gen1 endpoint zone; exact axis remains H5 evidence",
    "voice": "contact 12 faces the antenna edge along the dedicated UHF corridor",
    "voice_v": "contact 12 faces the antenna edge along the dedicated VHF corridor",
}

DIRECTIONAL_BODY_DIRECTIONS = {
    **INTERNAL_CONNECTOR_ACTUATOR_DIRECTIONS,
    **{
        instance: f"{face} {side} enclosure exit"
        for instance, face, side, _, _ in EDGE_INTERFACES
    },
    **{
        instance: f"{face} {side} labelled internal acoustic component"
        for instance, face, side, _, _ in EXTERNAL_COMPONENT_LABELS
    },
    **{item.instance: "front-normal outward actuation" for item in FRONT_CONTROLS},
    **{item.instance: "rear-normal outward actuation" for item in REAR_CONTROLS},
    **{item.instance: "rear-normal outward actuation" for item in REAR_SELECTED_ACTUATORS},
    "microphone": "bottom enclosure exit; physical body on RF-inner; user silkscreen on front-outer",
    "u214_connector": "rear-normal outward mating into the removable Cap",
}

EXTERIOR_BODY_CONTRACTS = (
    BodyProjectionContract("display", "front-outer", 0, "front-normal outward view/touch"),
    BodyProjectionContract("u214", "rear-outer", 0, "rear-normal dock mating/removal"),
    BodyProjectionContract("pack_holder", "rear-outer", 90, "rear-normal open-cell access"),
    BodyProjectionContract("pack_cell0", "rear-outer", 90, "rear-normal cell insertion/removal"),
    BodyProjectionContract("pack_cell1", "rear-outer", 90, "rear-normal cell insertion/removal"),
    *(
        BodyProjectionContract(
            RF_INSTANCE_BY_PATH[path],
            "front-outer",
            0,
            "toward the antenna edge along board -Y",
        )
        for _, path, _ in FRONT_RF
    ),
    *(
        BodyProjectionContract(
            RF_INSTANCE_BY_PATH[path],
            "rear-outer",
            0,
            "toward the antenna edge along board -Y",
        )
        for _, path, _ in REAR_RF
    ),
    *(
        BodyProjectionContract(instance, "front-outer", 0, "front-normal optical emission")
        for instance, _, _, _ in FRONT_FACE_INDICATORS
    ),
    *(
        BodyProjectionContract(route.instance, "ui-inner-route", 0, "module-to-board RF cable path")
        for route in UI_RF_CABLES
    ),
    *(
        BodyProjectionContract(
            reserve.instance,
            "rf-inner-route",
            0,
            "bounded module-face zone to fixed Gen1 board receptacle; H5 locks the conservative corridor and H7/H8 inspect the received axis after arrival",
        )
        for reserve in RF_NRF_CABLE_RESERVES
    ),
    BodyProjectionContract(
        "display_touch_controller",
        "display-assembly",
        0,
        "superseded H2 controller node; the H1 physical endpoint contains exact ILI9488 and FT6236 identities without a separate host-board body",
    ),
)


def load() -> tuple[dict, dict, dict, dict, dict, dict]:
    devices = json.loads(DEVICES_PATH.read_text(encoding="utf-8"))["devices"]
    candidate = json.loads(CANDIDATE_PATH.read_text(encoding="utf-8"))
    navigation_cluster = json.loads(NAVIGATION_CLUSTER_PATH.read_text(encoding="utf-8"))
    display_mount_design = json.loads(DISPLAY_MOUNT_DESIGN_PATH.read_text(encoding="utf-8"))
    assembly_coordinate_model = json.loads(ASSEMBLY_COORDINATE_MODEL_PATH.read_text(encoding="utf-8"))
    instances = dict(candidate["instances"])
    # H1-R2.39 owns the physical display endpoint.  The reviewed G2F-3I
    # electrical candidate remains the superseded H2 input until the next
    # phase rewires its display sheet to the accepted direct 50-contact map.
    instances["display"] = "eastrising_er_tft035ips_6_ctp"
    instances["display_connector"] = "hirose_fh34srj_50s_0_5sh_50"
    instances.pop("display_adapter_plug", None)
    instances.pop("display_panel_connector", None)
    return (
        devices, candidate, instances, navigation_cluster,
        display_mount_design, assembly_coordinate_model,
    )


def placement_size(item: Placement, devices: dict, instances: dict) -> tuple[float, float]:
    device = devices[instances[item.instance]]
    dimensions = device.get("maximum_dimensions_mm", device.get("dimensions_mm"))
    if not dimensions or len(dimensions) < 2 or dimensions[0] is None or dimensions[1] is None:
        raise ValueError(f"{item.instance}: two-dimensional package envelope is missing")
    w, h = float(dimensions[0]), float(dimensions[1])
    angle = math.radians(item.rotation % 180)
    return (
        abs(w * math.cos(angle)) + abs(h * math.sin(angle)),
        abs(w * math.sin(angle)) + abs(h * math.cos(angle)),
    )


def placed_contact_xy(
    item: Placement, device: dict, contact_xy: tuple[float, float]
) -> tuple[float, float]:
    """Transform a manufacturer top-left contact coordinate into board space."""
    width, height = map(float, device["dimensions_mm"][:2])
    contact_x, contact_y = contact_xy
    rotation = item.rotation % 360
    if rotation == 0:
        local_x, local_y = contact_x, contact_y
    elif rotation == 90:
        local_x, local_y = height - contact_y, contact_x
    elif rotation == 180:
        local_x, local_y = width - contact_x, height - contact_y
    elif rotation == 270:
        local_x, local_y = contact_y, width - contact_x
    else:
        raise ValueError(f"{item.instance}: unsupported contact rotation {rotation}")
    return item.x + local_x, item.y + local_y


def placement_height(item: Placement, devices: dict, instances: dict) -> float:
    """Return the manufacturer-backed body height recorded for a placed part."""
    device = devices[instances[item.instance]]
    dimensions = device.get("maximum_dimensions_mm", device.get("dimensions_mm"))
    if not dimensions or len(dimensions) < 3 or dimensions[2] is None:
        raise ValueError(f"{item.instance}: package height is missing")
    height = float(dimensions[2])
    if height <= 0:
        raise ValueError(f"{item.instance}: package height must be positive")
    return height


def encoder_through_board_features(
    devices: dict,
    instances: dict,
) -> tuple[ThroughBoardFeature, ...]:
    """Project the exact EC11E mounting tabs and five terminals into the gap."""
    encoder = next(item for item in REAR_CONTROLS if item.instance == "encoder")
    if encoder.rotation != 0:
        raise ValueError("encoder through-board feature map currently requires drawing orientation 0")
    width, height = placement_size(encoder, devices, instances)
    center_x = encoder.x + width / 2
    center_y = encoder.y + height / 2
    contract = devices[instances["encoder"]]["mechanical_contract"]
    inner_height = float(contract["inner_terminal_projection_mm"])
    dummy_w, dummy_h = map(float, contract["maximum_dummy_terminal_hole_mm"])
    pin_d = float(contract["maximum_signal_terminal_hole_diameter_mm"])
    rows: list[ThroughBoardFeature] = []
    for index, (dx, dy) in enumerate(contract["dummy_terminal_centres_mm"], 1):
        rows.append(
            ThroughBoardFeature(
                "encoder", f"dummy_terminal_{index}",
                center_x + float(dx) - dummy_w / 2,
                center_y + float(dy) - dummy_h / 2,
                dummy_w, dummy_h, inner_height,
                "EC11E mechanical terminal and maximum mounting-hole envelope",
            )
        )
    for names, key in (
        (("D", "E"), "switch_terminal_centres_mm"),
        (("A", "C", "B"), "encoder_terminal_centres_mm"),
    ):
        for name, (dx, dy) in zip(names, contract[key]):
            rows.append(
                ThroughBoardFeature(
                    "encoder", f"contact_{name}",
                    center_x + float(dx) - pin_d / 2,
                    center_y + float(dy) - pin_d / 2,
                    pin_d, pin_d, inner_height,
                    "EC11E electrical terminal and maximum plated-hole envelope",
                )
            )
    return tuple(rows)


def nrf_cable_reserve_module_box(
    reserve: CableReserve,
    devices: dict,
    instances: dict,
) -> tuple[float, float, float, float]:
    module = next(item for item in RF_INNER if item.instance == reserve.module_instance)
    width, height = placement_size(module, devices, instances)
    return module.x, module.y, width, height


def interboard_individual_clearances(
    devices: dict,
    instances: dict,
) -> list[tuple[float, Placement]]:
    """Return each inner body's remaining distance to the opposite PCB plane."""
    rows = [
        (INTERBOARD_GAP_MM - placement_height(item, devices, instances), item)
        for item in UI_INNER + RF_INNER
    ]
    return sorted(rows, key=lambda row: (row[0], row[1].instance))


def mirrored_x(x: float, width: float = 0.0) -> float:
    """Mirror a point or left edge across the 80-mm board centreline."""
    return BOARD_W - x - width


def overlaps(a: tuple[float, float, float, float], b: tuple[float, float, float, float], margin: float = 0.0) -> bool:
    ax, ay, aw, ah = a
    bx, by, bw, bh = b
    return ax < bx + bw + margin and bx < ax + aw + margin and ay < by + bh + margin and by < ay + ah + margin


def interboard_clearance_pairs(
    devices: dict,
    instances: dict,
) -> list[tuple[float, Placement, Placement]]:
    """Calculate every non-mating pair projected into the same physical datum.

    Placement X is authored as seen from each board's external face.  The rear
    RF/power board therefore has to be mirrored into the front-board datum
    before the two inner faces can be compared.
    """
    pairs: list[tuple[float, Placement, Placement]] = []
    for ui_item in UI_INNER:
        ui_w, ui_h = placement_size(ui_item, devices, instances)
        ui_box = (ui_item.x, ui_item.y, ui_w, ui_h)
        for rf_item in RF_INNER:
            rf_w, rf_h = placement_size(rf_item, devices, instances)
            rf_box = (mirrored_x(rf_item.x, rf_w), rf_item.y, rf_w, rf_h)
            if not overlaps(ui_box, rf_box):
                continue
            if (ui_item.instance, rf_item.instance) in INTENTIONAL_INTERBOARD_MATES:
                continue
            clearance = (
                INTERBOARD_GAP_MM
                - placement_height(ui_item, devices, instances)
                - placement_height(rf_item, devices, instances)
            )
            pairs.append((clearance, ui_item, rf_item))
    return sorted(pairs, key=lambda row: (row[0], row[1].instance, row[2].instance))


def display_mount_opposing_clearance_pairs(
    design: dict,
    devices: dict,
    instances: dict,
) -> list[tuple[float, Placement]]:
    """Check the direct display ZIF envelope against the opposing RF-inner face."""
    row = design["components"][0]
    connector_x, connector_y = map(float, row["ui_inner_position_mm"])
    connector_w, connector_h, connector_z = map(float, row["envelope_mm"])
    connector_box = (connector_x, connector_y, connector_w, connector_h)
    rows: list[tuple[float, Placement]] = []
    for rf_item in RF_INNER:
        rf_w, rf_h = placement_size(rf_item, devices, instances)
        rf_box = (mirrored_x(rf_item.x, rf_w), rf_item.y, rf_w, rf_h)
        if overlaps(connector_box, rf_box):
            rows.append(
                (
                    INTERBOARD_GAP_MM
                    - connector_z
                    - placement_height(rf_item, devices, instances),
                    rf_item,
                )
            )
    return sorted(rows, key=lambda row: (row[0], row[1].instance))


def hits_hole(
    rectangle: tuple[float, float, float, float],
    hole: tuple[float, float],
    clearance: float = 0.0,
) -> bool:
    x, y, w, h = rectangle
    hx, hy = hole
    px = min(max(hx, x), x + w)
    py = min(max(hy, y), y + h)
    return math.hypot(hx - px, hy - py) < MOUNT_KEEPOUT_R + clearance


def polyline_length(points: tuple[tuple[float, float], ...]) -> float:
    return sum(
        math.hypot(x2 - x1, y2 - y1)
        for (x1, y1), (x2, y2) in zip(points, points[1:])
    )


def point_segment_distance(
    point: tuple[float, float],
    start: tuple[float, float],
    end: tuple[float, float],
) -> float:
    px, py = point
    x1, y1 = start
    x2, y2 = end
    dx, dy = x2 - x1, y2 - y1
    denominator = dx * dx + dy * dy
    if denominator == 0:
        return math.hypot(px - x1, py - y1)
    amount = max(0.0, min(1.0, ((px - x1) * dx + (py - y1) * dy) / denominator))
    return math.hypot(px - (x1 + amount * dx), py - (y1 + amount * dy))


def axis_aligned_segment_hits_box(
    start: tuple[float, float],
    end: tuple[float, float],
    rectangle: tuple[float, float, float, float],
    margin: float = 0.0,
) -> bool:
    """Return whether a horizontal/vertical route corridor meets a box."""
    x1, y1 = start
    x2, y2 = end
    x, y, w, h = rectangle
    left, right = x - margin, x + w + margin
    top, bottom = y - margin, y + h + margin
    if abs(y1 - y2) < 0.001:
        return top <= y1 <= bottom and max(min(x1, x2), left) <= min(max(x1, x2), right)
    if abs(x1 - x2) < 0.001:
        return left <= x1 <= right and max(min(y1, y2), top) <= min(max(y1, y2), bottom)
    raise ValueError(f"non-orthogonal cable segment {start}/{end}")


def segment_hits_box(
    start: tuple[float, float],
    end: tuple[float, float],
    rectangle: tuple[float, float, float, float],
    margin: float = 0.0,
) -> bool:
    """Return whether any straight segment meets an expanded axis-aligned box."""
    x, y, w, h = rectangle
    left, right = x - margin, x + w + margin
    top, bottom = y - margin, y + h + margin
    x1, y1 = start
    x2, y2 = end
    dx, dy = x2 - x1, y2 - y1
    lower, upper = 0.0, 1.0
    for direction, near_delta, far_delta in (
        (dx, x1 - left, right - x1),
        (dy, y1 - top, bottom - y1),
    ):
        if abs(direction) < 1e-12:
            if near_delta < 0 or far_delta < 0:
                return False
            continue
        first = -near_delta / direction
        second = far_delta / direction
        if first > second:
            first, second = second, first
        lower = max(lower, first)
        upper = min(upper, second)
        if lower > upper:
            return False
    return True


def cable_interboard_clearance_pairs(
    devices: dict,
    instances: dict,
) -> list[tuple[float, CableRoute, Placement]]:
    """Calculate cable/body pairs that overlap across the inner channel."""
    pairs: list[tuple[float, CableRoute, Placement]] = []
    for route in UI_RF_CABLES:
        device = devices[instances[route.instance]]
        cable_od = float(device["electrical_contract"]["cable_outer_diameter_mm"])
        cable_radius = cable_od / 2
        for rf_item in RF_INNER:
            rf_w, rf_h = placement_size(rf_item, devices, instances)
            rf_box = (mirrored_x(rf_item.x, rf_w), rf_item.y, rf_w, rf_h)
            if any(
                segment_hits_box(start, end, rf_box, cable_radius)
                for start, end in zip(route.points, route.points[1:])
            ):
                clearance = (
                    INTERBOARD_GAP_MM
                    - cable_od
                    - placement_height(rf_item, devices, instances)
                )
                pairs.append((clearance, route, rf_item))
    return sorted(pairs, key=lambda row: (row[0], row[1].instance, row[2].instance))


def nrf_cable_reserve_opposing_pairs(
    devices: dict,
    instances: dict,
) -> list[tuple[float, CableReserve, Placement]]:
    """Check the same-board RF-inner cable reserves against UI bodies."""
    pairs: list[tuple[float, CableReserve, Placement]] = []
    for reserve in RF_NRF_CABLE_RESERVES:
        cable = devices[instances[reserve.instance]]
        cable_contract = cable["electrical_contract"]
        radius = float(
            cable_contract.get("cable_outer_diameter_mm", cable_contract["cable_outer_diameter_mm_max"])
        ) / 2
        occupied_height = max(
            float(cable["mechanical_contract"]["maximum_mated_height_mm"]),
            placement_height(
                next(item for item in RF_INNER if item.instance == reserve.module_instance),
                devices,
                instances,
            ),
        )
        module_box = nrf_cable_reserve_module_box(reserve, devices, instances)
        for ui_item in UI_INNER:
            ui_w, ui_h = placement_size(ui_item, devices, instances)
            ui_box = (mirrored_x(ui_item.x, ui_w), ui_item.y, ui_w, ui_h)
            if overlaps(module_box, ui_box) or any(
                segment_hits_box(start, end, ui_box, radius)
                for start, end in zip(reserve.escape_points, reserve.escape_points[1:])
            ):
                clearance = (
                    INTERBOARD_GAP_MM
                    - occupied_height
                    - placement_height(ui_item, devices, instances)
                )
                pairs.append((clearance, reserve, ui_item))
    return sorted(pairs, key=lambda row: (row[0], row[1].instance, row[2].instance))


def through_board_opposing_pairs(
    devices: dict,
    instances: dict,
) -> list[tuple[float, ThroughBoardFeature, Placement]]:
    """Check exterior THT terminals protruding into the gap against UI bodies."""
    pairs: list[tuple[float, ThroughBoardFeature, Placement]] = []
    for feature in encoder_through_board_features(devices, instances):
        feature_box = (feature.x, feature.y, feature.w, feature.h)
        for ui_item in UI_INNER:
            ui_w, ui_h = placement_size(ui_item, devices, instances)
            ui_box = (mirrored_x(ui_item.x, ui_w), ui_item.y, ui_w, ui_h)
            if overlaps(feature_box, ui_box):
                clearance = (
                    INTERBOARD_GAP_MM
                    - feature.inner_height
                    - placement_height(ui_item, devices, instances)
                )
                pairs.append((clearance, feature, ui_item))
    return sorted(pairs, key=lambda row: (row[0], row[1].feature, row[2].instance))


def text_bounds_px(element: ET.Element) -> tuple[float, float, float, float]:
    """Conservative sans-serif bounds for generated silkscreen text."""
    x = float(element.attrib["x"])
    baseline = float(element.attrib["y"])
    size = float(element.attrib["font-size"])
    value = "".join(element.itertext())
    width = max(size * 0.6, len(value) * size * 0.58)
    anchor = element.attrib.get("text-anchor", "start")
    if anchor == "middle":
        left = x - width / 2
    elif anchor == "end":
        left = x - width
    else:
        left = x
    return left, baseline - size, width, size * 1.25


def validate_external_silkscreen(svg: str, devices: dict, instances: dict) -> list[str]:
    """Prove that every physical silk label is on an outer face and unobscured."""
    errors: list[str] = []
    scale = 3.7
    origins = {"front": (80.0, 150.0), "rear": (465.0, 150.0)}

    def px_box(origin, box):
        x, y, w, h = box
        return origin[0] + x * scale, origin[1] + y * scale, w * scale, h * scale

    display = Placement("display", DISPLAY_X, DISPLAY_Y, "display")
    holder = Placement("pack_holder", PACK_HOLDER_DRAWING_X, PACK_HOLDER_Y, "holder", 90)
    knob = REAR_SELECTED_ACTUATORS[0]
    visible = {
        "front": [
            ("display", (display.x, display.y, *placement_size(display, devices, instances))),
            *(
                (item.instance, (item.x, item.y, *placement_size(item, devices, instances)))
                for item in FRONT_CONTROLS
                if item.instance in DIRECT_PRESS_FRONT_CONTROLS
            ),
            *((reserve.name, (reserve.x, reserve.y, reserve.w, reserve.h)) for reserve in FRONT_CAP_RESERVES),
            *((label + " LED", (x, y, TX_LED_W, TX_LED_H)) for _, label, x, y in FRONT_FACE_INDICATORS),
        ],
        "rear": [
            ("U214", (U214_X, U214_Y, U214_W, U214_H)),
            ("battery holder", (holder.x, holder.y, *placement_size(holder, devices, instances))),
            *((item.instance, (item.x, item.y, *placement_size(item, devices, instances))) for item in REAR_CONTROLS),
            ("encoder knob", (knob.x, knob.y, *placement_size(knob, devices, instances))),
            *((reserve.name, (reserve.x, reserve.y, reserve.w, reserve.h)) for reserve in REAR_CAP_RESERVES),
        ],
    }
    for face, bank in (("front", FRONT_RF), ("rear", REAR_RF)):
        visible[face].extend(
            (f"{path} connector", (centre - RF_BODY_W / 2, 0.0, RF_BODY_W, RF_BODY_D))
            for centre, path, _ in bank
        )
    for face in visible:
        visible[face].extend(
            (f"M2.5 keep-out {index}", (hx - MOUNT_KEEPOUT_R, hy - MOUNT_KEEPOUT_R, 2 * MOUNT_KEEPOUT_R, 2 * MOUNT_KEEPOUT_R))
            for index, (hx, hy) in enumerate(HOLES, 1)
        )

    root = ET.fromstring(svg)
    labels: dict[str, list[tuple[str, tuple[float, float, float, float]]]] = {"front": [], "rear": []}
    for element in root.iter("{http://www.w3.org/2000/svg}text"):
        if element.attrib.get("data-layer") != "pcb-silkscreen":
            continue
        value = "".join(element.itertext())
        box = text_bounds_px(element)
        face = next(
            (
                name
                for name, origin in origins.items()
                if origin[0] <= box[0]
                and box[0] + box[2] <= origin[0] + BOARD_W * scale
                and origin[1] <= box[1]
                and box[1] + box[3] <= origin[1] + BOARD_H * scale
            ),
            None,
        )
        if face is None:
            errors.append(f"external silk '{value}' is not wholly inside an outer PCB face")
            continue
        labels[face].append((value, box))
        for component, component_mm in visible[face]:
            if overlaps(box, px_box(origins[face], component_mm)):
                errors.append(f"{face}: silk '{value}' overlaps {component}")

    for face, face_labels in labels.items():
        for index, (value, box) in enumerate(face_labels):
            for other_value, other_box in face_labels[index + 1:]:
                if overlaps(box, other_box):
                    errors.append(f"{face}: silk '{value}' overlaps silk '{other_value}'")
    if not labels["front"] or not labels["rear"]:
        errors.append("both outer PCB faces must carry their generated user silkscreen labels")
    return errors


def validate_items(name: str, items: tuple[Placement, ...], devices: dict, instances: dict) -> list[str]:
    errors: list[str] = []
    rectangles = []
    for item in items:
        if item.instance not in instances:
            errors.append(f"{name}: unknown instance {item.instance}")
            continue
        try:
            w, h = placement_size(item, devices, instances)
        except ValueError as error:
            errors.append(str(error))
            continue
        rectangle = (item.x, item.y, w, h)
        rectangles.append((item, rectangle))
        if item.x < 0 or item.y < 0 or item.x + w > BOARD_W + 0.001 or item.y + h > BOARD_H + 0.001:
            errors.append(f"{name}: {item.instance} is outside the 80x150-mm board")
        for hole in HOLES:
            if hits_hole(rectangle, hole):
                errors.append(f"{name}: {item.instance} enters the M2.5 keep-out at {hole}")
    for index, (left, left_box) in enumerate(rectangles):
        for right, right_box in rectangles[index + 1:]:
            if overlaps(left_box, right_box, 0.7):
                errors.append(f"{name}: {left.instance} overlaps {right.instance}")
    return errors


def cap_evidence_coordinate_register_audit(
    devices: dict,
    instances: dict,
    projection_groups: tuple[tuple[str, tuple[Placement, ...]], ...] | None = None,
) -> dict:
    """Resolve the exact current-G2F Cap/evidence placement manifest.

    The 0.35-mm per-side placement courtyard is the conservative collision
    envelope used by the H1 paper model (equivalent to the existing 0.7-mm
    body-to-body rule). It is not an ECAD land-pattern claim.
    """
    projected: dict[str, list[tuple[str, Placement]]] = {}
    for frame, items in projection_groups or PLACEMENT_PROJECTION_GROUPS:
        for item in items:
            projected.setdefault(item.instance, []).append((frame, item))
    errors: list[str] = []
    rows = []
    for instance, expected_device_key in sorted(
        CAP_EVIDENCE_COORDINATE_INSTANCE_DEVICES.items()
    ):
        actual_device_key = instances.get(instance)
        if actual_device_key != expected_device_key:
            errors.append(
                f"cap-evidence-register: {instance} expected current G2F device "
                f"{expected_device_key}, got {actual_device_key}"
            )
            continue
        occurrences = projected.get(instance, [])
        if len(occurrences) != 1:
            errors.append(
                f"cap-evidence-register: {instance} has {len(occurrences)} physical projections; expected one"
            )
            continue
        frame, item = occurrences[0]
        expected_frame = "rear-outer" if instance == "u214_connector" else "rf-inner"
        if frame != expected_frame:
            errors.append(
                f"cap-evidence-register: {instance} is in {frame}; expected {expected_frame}"
            )
            continue
        try:
            width, height = placement_size(item, devices, instances)
        except ValueError as error:
            errors.append(f"cap-evidence-register: {error}")
            continue
        device = devices[actual_device_key]
        source = device.get("mechanical_source", device.get("source", {}))
        if not source.get("document") or not source.get("url"):
            errors.append(f"cap-evidence-register: {instance} lacks source-backed envelope evidence")
            continue
        halo = CAP_EVIDENCE_COURTYARD_HALO_MM
        rows.append(
            {
                "instance": instance,
                "device_key": actual_device_key,
                "mpn": device["mpn"],
                "frame": frame,
                "coordinate_mm": [item.x, item.y],
                "rotation_deg": item.rotation,
                "source_envelope_mm": [width, height],
                "placement_courtyard_bbox_mm": {
                    "x": [round(item.x - halo, 6), round(item.x + width + halo, 6)],
                    "y": [round(item.y - halo, 6), round(item.y + height + halo, 6)],
                },
                "source": {
                    field: source[field]
                    for field in ("document", "version", "url", "checked")
                    if field in source
                },
            }
        )
    return {
        "status": "pass" if not errors else "fail",
        "candidate_id": "G2F-3I",
        "policy": (
            "exact current-G2F identity; exactly one physical coordinate; "
            "source body envelope plus 0.35-mm per-side H1 collision halo; "
            "H2 retains trace order and the connector-side ESD launch constraint"
        ),
        "courtyard_halo_per_side_mm": CAP_EVIDENCE_COURTYARD_HALO_MM,
        "expected_instance_count": len(CAP_EVIDENCE_COORDINATE_INSTANCE_DEVICES),
        "resolved_instance_count": len(rows),
        "instances": rows,
        "errors": errors,
    }


def validate_cable_routes(devices: dict, instances: dict) -> list[str]:
    errors: list[str] = []
    ui_by_instance = {item.instance: item for item in UI_INNER}
    module_by_route = {
        "s3_rf_jumper": ("s3", "s3_rf_board_connector"),
        "c5_rf_jumper": ("c5", "c5_rf_board_connector"),
    }
    for route in UI_RF_CABLES:
        if route.instance not in instances:
            errors.append(f"native-rf-cable: unknown instance {route.instance}")
            continue
        device = devices[instances[route.instance]]
        expected_length = float(device["electrical_contract"]["cable_length_mm"])
        projected_length = polyline_length(route.points)
        if len(route.points) != 2:
            errors.append(
                f"native-rf-cable: {route.instance} must render as one direct connector-to-connector projection"
            )
        if projected_length >= expected_length:
            errors.append(
                f"native-rf-cable: {route.instance} {projected_length:.2f}-mm connector chord "
                f"cannot fit the selected {expected_length:.2f}-mm assembly"
            )
        cable_radius = float(device["electrical_contract"]["cable_outer_diameter_mm"]) / 2
        cable_od = cable_radius * 2
        if INTERBOARD_GAP_MM - cable_od < MIN_INTERBOARD_Z_CLEARANCE_MM:
            errors.append(f"native-rf-cable: {route.instance} does not fit the interboard channel")
        for point in route.points:
            if not (cable_radius <= point[0] <= BOARD_W - cable_radius and cable_radius <= point[1] <= BOARD_H - cable_radius):
                errors.append(f"native-rf-cable: {route.instance} leaves the PCB plan at {point}")
        for segment in zip(route.points, route.points[1:]):
            for hole in HOLES:
                if point_segment_distance(hole, *segment) < MOUNT_KEEPOUT_R + cable_radius:
                    errors.append(f"native-rf-cable: {route.instance} enters the M2.5 keep-out at {hole}")

        module_instance, board_connector_instance = module_by_route[route.instance]
        module = ui_by_instance[module_instance]
        module_rf = devices[instances[module_instance]]["rf_connector"]["center_from_module_top_left_mm"]
        expected_start = (module.x + float(module_rf[0]), module.y + float(module_rf[1]))
        connector = ui_by_instance[board_connector_instance]
        connector_w, connector_h = placement_size(connector, devices, instances)
        expected_end = (connector.x + connector_w / 2, connector.y + connector_h / 2)
        if any(abs(a - b) > 0.01 for a, b in zip(route.points[0], expected_start)):
            errors.append(f"native-rf-cable: {route.instance} does not start at the official module RF axis")
        if any(abs(a - b) > 0.01 for a, b in zip(route.points[-1], expected_end)):
            errors.append(f"native-rf-cable: {route.instance} does not end at its board receptacle axis")

        allowed_contacts = {module_instance, board_connector_instance}
        for item in UI_INNER:
            if item.instance in allowed_contacts:
                continue
            item_w, item_h = placement_size(item, devices, instances)
            item_box = (item.x, item.y, item_w, item_h)
            route_hits = any(
                segment_hits_box(
                    start,
                    end,
                    item_box,
                    cable_radius + MIN_INTERBOARD_Z_CLEARANCE_MM,
                )
                for start, end in zip(route.points, route.points[1:])
            )
            if route_hits:
                errors.append(
                    f"native-rf-cable: {route.instance} lacks {MIN_INTERBOARD_Z_CLEARANCE_MM:.1f}-mm "
                    f"same-face clearance to {item.instance}"
                )

    if {route.instance for route in UI_RF_CABLES} != {"s3_rf_jumper", "c5_rf_jumper"}:
        errors.append("native-rf-cable: exact S3 and C5 jumper routes must both be present")
    for clearance, route, rf_item in cable_interboard_clearance_pairs(devices, instances):
        if clearance < MIN_INTERBOARD_Z_CLEARANCE_MM:
            errors.append(
                f"native-rf-cable: {route.instance}/{rf_item.instance} leaves only "
                f"{clearance:.2f} mm across the interboard channel"
            )
    return errors


def validate_nrf_cable_reserves(devices: dict, instances: dict) -> list[str]:
    """Validate conservative RF-inner module-face reserves for all three nRF jumpers."""
    errors: list[str] = []
    rf_by_instance = {item.instance: item for item in RF_INNER}
    expected = {f"nrf{index}_rf_jumper" for index in range(3)}
    if {reserve.instance for reserve in RF_NRF_CABLE_RESERVES} != expected:
        errors.append("nrf-rf-cable: all three conservative jumper reserves must be present")
    for reserve in RF_NRF_CABLE_RESERVES:
        cable = devices[instances[reserve.instance]]
        contract = cable["electrical_contract"]
        mechanical = cable["mechanical_contract"]
        exact_length = float(contract["cable_length_mm"])
        cable_radius = float(
            contract.get("cable_outer_diameter_mm", contract["cable_outer_diameter_mm_max"])
        ) / 2
        plug_plan = list(map(float, mechanical.get("maximum_plug_plan_envelope_mm", [])))
        if len(plug_plan) != 2 or plug_plan != [3.0, 3.1]:
            errors.append(f"nrf-rf-cable: {reserve.instance} lacks the exact Gen1 plug plan envelope")
        escape_length = polyline_length(reserve.escape_points)
        if not 0 < escape_length < exact_length:
            errors.append(f"nrf-rf-cable: {reserve.instance} escape cannot retain cable slack")
        if len(reserve.escape_points) != 2:
            errors.append(
                f"nrf-rf-cable: {reserve.instance} must render as one direct IPEX-zone-to-U.FL projection"
            )
        module = rf_by_instance[reserve.module_instance]
        connector = rf_by_instance[reserve.board_connector_instance]
        module_box = nrf_cable_reserve_module_box(reserve, devices, instances)
        module_x, module_y, module_w, module_h = module_box
        first_x, first_y = reserve.escape_points[0]
        on_module_edge = (
            module_x - 0.01 <= first_x <= module_x + module_w + 0.01
            and module_y - 0.01 <= first_y <= module_y + module_h + 0.01
            and (
                abs(first_x - module_x) <= 0.01
                or abs(first_x - (module_x + module_w)) <= 0.01
                or abs(first_y - module_y) <= 0.01
                or abs(first_y - (module_y + module_h)) <= 0.01
            )
        )
        if not on_module_edge:
            errors.append(f"nrf-rf-cable: {reserve.instance} escape does not start on its module face")
        connector_w, connector_h = placement_size(connector, devices, instances)
        expected_end = (connector.x + connector_w / 2, connector.y + connector_h / 2)
        if any(abs(a - b) > 0.01 for a, b in zip(reserve.escape_points[-1], expected_end)):
            errors.append(f"nrf-rf-cable: {reserve.instance} escape misses its exact board receptacle")
        allowed = {reserve.module_instance, reserve.board_connector_instance}
        for segment in zip(reserve.escape_points, reserve.escape_points[1:]):
            for hole in HOLES:
                if point_segment_distance(hole, *segment) < MOUNT_KEEPOUT_R + cable_radius:
                    errors.append(f"nrf-rf-cable: {reserve.instance} enters the M2.5 keep-out at {hole}")
            for item in RF_INNER:
                if item.instance in allowed:
                    continue
                item_w, item_h = placement_size(item, devices, instances)
                if segment_hits_box(
                    *segment,
                    (item.x, item.y, item_w, item_h),
                    cable_radius + MIN_INTERBOARD_Z_CLEARANCE_MM,
                ):
                    errors.append(
                        f"nrf-rf-cable: {reserve.instance} escape lacks "
                        f"{MIN_INTERBOARD_Z_CLEARANCE_MM:.1f}-mm clearance to {item.instance}"
                    )
        for point in reserve.escape_points:
            if not (
                cable_radius <= point[0] <= BOARD_W - cable_radius
                and cable_radius <= point[1] <= BOARD_H - cable_radius
            ):
                errors.append(f"nrf-rf-cable: {reserve.instance} escape leaves the PCB plan at {point}")
        # The unknown current-lot axis may be anywhere in the module face.  The
        # controlled plug footprint is reserved inside that complete face; its
        # actual axis, bend and retention remain the already-declared H5 gate.
        if module_w < max(plug_plan or [999]) or module_h < max(plug_plan or [999]):
            errors.append(f"nrf-rf-cable: {reserve.instance} module face cannot contain its plug")
    for clearance, reserve, ui_item in nrf_cable_reserve_opposing_pairs(devices, instances):
        if clearance < MIN_INTERBOARD_Z_CLEARANCE_MM:
            errors.append(
                f"nrf-rf-cable: {reserve.instance}/{ui_item.instance} leaves only "
                f"{clearance:.2f} mm across the interboard channel"
            )
    return errors


def validate_through_board_features(devices: dict, instances: dict) -> list[str]:
    """Validate THT tails that enter the gap from an externally mounted part."""
    errors: list[str] = []
    features = encoder_through_board_features(devices, instances)
    if len(features) != 7:
        errors.append("through-board: EC11E must expose two tabs and five terminal tails")
    for feature in features:
        feature_box = (feature.x, feature.y, feature.w, feature.h)
        if (
            feature.x < 0
            or feature.y < 0
            or feature.x + feature.w > BOARD_W
            or feature.y + feature.h > BOARD_H
        ):
            errors.append(f"through-board: encoder {feature.feature} leaves the PCB plan")
        if feature.inner_height + MIN_INTERBOARD_Z_CLEARANCE_MM > INTERBOARD_GAP_MM:
            errors.append(f"through-board: encoder {feature.feature} exceeds the 11-mm channel")
        for item in RF_INNER:
            item_w, item_h = placement_size(item, devices, instances)
            if overlaps(
                feature_box,
                (item.x, item.y, item_w, item_h),
                MIN_INTERBOARD_Z_CLEARANCE_MM,
            ):
                errors.append(
                    f"through-board: encoder {feature.feature} conflicts with {item.instance}"
                )
        for zone in INTERNAL_RESERVES:
            if overlaps(
                feature_box,
                (zone.x, zone.y, zone.w, zone.h),
                MIN_INTERBOARD_Z_CLEARANCE_MM,
            ):
                errors.append(f"through-board: encoder {feature.feature} conflicts with {zone.name}")
    for clearance, feature, ui_item in through_board_opposing_pairs(devices, instances):
        if clearance < MIN_INTERBOARD_Z_CLEARANCE_MM:
            errors.append(
                f"through-board: encoder {feature.feature}/{ui_item.instance} leaves only "
                f"{clearance:.2f} mm across the interboard channel"
            )
    return errors


def validate_reserves(name: str, reserves: tuple[Reserve, ...]) -> list[str]:
    errors: list[str] = []
    for reserve in reserves:
        if reserve.reserve_class not in {
            "custom_actuator", "custom_enclosure_geometry", "unselected_bom_part",
            "selected_support_placement_zone",
        }:
            errors.append(f"{name}: {reserve.name} has invalid reserve class {reserve.reserve_class}")
        rectangle = (reserve.x, reserve.y, reserve.w, reserve.h)
        if reserve.x < 0 or reserve.y < 0 or reserve.x + reserve.w > BOARD_W or reserve.y + reserve.h > BOARD_H:
            errors.append(f"{name}: {reserve.name} is outside the 80x150-mm board")
        for hole in HOLES:
            if hits_hole(rectangle, hole):
                errors.append(f"{name}: {reserve.name} enters the M2.5 keep-out at {hole}")
    return errors


def mechanical_body_contracts() -> tuple[dict[str, BodyProjectionContract], list[str]]:
    """Build one traceable datum/orientation/direction contract per body."""
    contracts: dict[str, BodyProjectionContract] = {}
    errors: list[str] = []

    def register(contract: BodyProjectionContract) -> None:
        if contract.instance in contracts:
            errors.append(f"mechanical-source: duplicate body contract for {contract.instance}")
            return
        contracts[contract.instance] = contract

    for frame, items in PLACEMENT_PROJECTION_GROUPS:
        if frame not in MECHANICAL_PROJECTION_FRAMES:
            errors.append(f"mechanical-source: unknown projection frame {frame}")
        for item in items:
            register(
                BodyProjectionContract(
                    item.instance,
                    frame,
                    item.rotation,
                    DIRECTIONAL_BODY_DIRECTIONS.get(item.instance, "not applicable"),
                )
            )
    for contract in EXTERIOR_BODY_CONTRACTS:
        register(contract)
    return contracts, errors


def validate_mechanical_sources(devices: dict, instances: dict) -> tuple[set[str], list[str]]:
    """Enforce the H1.1.2 manufacturer-envelope and projection contract."""
    contracts, errors = mechanical_body_contracts()
    expected = (
        {
            item.instance
            for _, items in PLACEMENT_PROJECTION_GROUPS
            for item in items
        }
        | MECHANICAL_ASSEMBLY_EMBEDDED_INSTANCES
        | MECHANICAL_EXTERIOR_INSTANCES
    )
    actual = set(contracts)
    if actual != expected:
        missing = ", ".join(sorted(expected - actual)) or "none"
        extra = ", ".join(sorted(actual - expected)) or "none"
        errors.append(f"mechanical-source: contract coverage differs; missing={missing}; extra={extra}")

    for instance, contract in contracts.items():
        if instance not in instances:
            errors.append(f"mechanical-source: unknown instance {instance}")
            continue
        device = devices[instances[instance]]
        mpn = device.get("mpn", "")
        if not isinstance(mpn, str) or not mpn.strip():
            errors.append(f"mechanical-source: {instance} has no exact MPN or explicit MPN TBD")
        if not device.get("qualification"):
            errors.append(f"mechanical-source: {instance} has no evidence qualification")

        dimensions = device.get("maximum_dimensions_mm", device.get("dimensions_mm"))
        if not isinstance(dimensions, list) or len(dimensions) < 3:
            errors.append(f"mechanical-source: {instance} lacks sourced LxWxH")
        elif any(value is None or float(value) <= 0 for value in dimensions[:3]):
            errors.append(f"mechanical-source: {instance} has a non-positive LxWxH envelope")

        source = device.get("mechanical_source", device.get("source", {}))
        for field in ("document", "url", "checked"):
            if not source.get(field):
                errors.append(f"mechanical-source: {instance} dimension source lacks {field}")
        if source.get("url") and not str(source["url"]).startswith("https://"):
            errors.append(f"mechanical-source: {instance} dimension source is not HTTPS")

        if contract.frame not in MECHANICAL_PROJECTION_FRAMES:
            errors.append(f"mechanical-source: {instance} has unknown datum frame {contract.frame}")
        if contract.rotation not in {0, 45, 90, 180, 270}:
            errors.append(f"mechanical-source: {instance} has unsupported orientation {contract.rotation}")
        if not contract.direction.strip():
            errors.append(f"mechanical-source: {instance} has no interface-direction classification")

    for instance, direction in DIRECTIONAL_BODY_DIRECTIONS.items():
        contract = contracts.get(instance)
        if contract is None:
            errors.append(f"mechanical-source: directional body {instance} is not rendered")
        elif contract.direction != direction:
            errors.append(f"mechanical-source: {instance} lost its explicit interface direction")
    return actual, errors


def validate_mechanical_evidence_gates(instances: dict, rendered: set[str]) -> list[str]:
    """Require one explicit H1/H5 disposition for every open physical fit."""
    data = json.loads(MECHANICAL_GATES_PATH.read_text(encoding="utf-8"))
    errors: list[str] = []
    if data.get("schema_version") != 1 or data.get("stage") != "H1.1.3":
        errors.append("mechanical-gates: schema/stage mismatch")
    constraint = data.get("execution_constraint", {})
    if constraint.get("status") != "research_first_active":
        errors.append("mechanical-gates: research-first evidence policy must remain explicit")
    if constraint.get("order_authorized") is not False:
        errors.append("mechanical-gates: H1 evidence ordering must remain unauthorized")
    if constraint.get("current_step") != "H2.3.4":
        errors.append("mechanical-gates: exact evidence-research substep drifted")

    gates = data.get("gates", [])
    identifiers = [gate.get("id") for gate in gates]
    if len(identifiers) != len(set(identifiers)) or any(not item for item in identifiers):
        errors.append("mechanical-gates: gate IDs must be present and unique")
    required_h1: set[str] = set()
    actual_h1 = {
        gate["id"] for gate in gates if gate.get("disposition") == "h1_blocker"
    }
    if actual_h1 != required_h1:
        errors.append("mechanical-gates: exact H1 blocker set is not classified")

    covered: set[str] = set()
    for gate in gates:
        if gate.get("disposition") not in {"h1_blocker", "h5_received_sample_gate"}:
            errors.append(f"mechanical-gates: {gate.get('id')} has invalid disposition")
        for field in ("evidence_boundary", "unknown", "closure", "blocks"):
            if not gate.get(field):
                errors.append(f"mechanical-gates: {gate.get('id')} lacks {field}")
        affected = gate.get("affected_instances", [])
        if not affected:
            errors.append(f"mechanical-gates: {gate.get('id')} has no affected instances")
        for instance in affected:
            covered.add(instance)
            if instance not in instances:
                errors.append(f"mechanical-gates: {gate.get('id')} names unknown {instance}")
            elif instance not in rendered:
                errors.append(f"mechanical-gates: {gate.get('id')} names unrendered {instance}")
        if gate.get("disposition") == "h5_received_sample_gate" and "H8" not in gate.get("blocks", []):
            errors.append(f"mechanical-gates: {gate.get('id')} must block H8")

    required_open_instances = {
        "display", "display_connector",
        "nrf0", "nrf1", "nrf2",
        "nrf0_rf_jumper", "nrf1_rf_jumper", "nrf2_rf_jumper",
        "nrf0_rf_board_connector", "nrf1_rf_board_connector", "nrf2_rf_board_connector",
        "nrf0_external_sma", "nrf1_external_sma", "nrf2_external_sma",
        "u214", "u214_connector",
        "ui_dpad_up", "ui_dpad_down", "ui_dpad_left", "ui_dpad_right", "ui_dpad_ok",
        "voice", "encoder", "encoder_knob", "power_command_switch",
        "ui_switch_back", "ui_switch_opt", "ui_switch_f1", "ui_switch_f2",
        "ui_switch_f3", "ui_switch_f4", "ui_switch_f5", "ui_switch_f6",
        "ui_switch_f7", "ui_switch_f8", "ptt_switch",
        "unit_connector", "pack_holder", "pack_cell0", "pack_cell1",
        "s3_rf_jumper", "c5_rf_jumper", "s3_rf_board_connector", "c5_rf_board_connector",
        "speaker", "microphone", "headphone_jack",
    }
    if not required_open_instances <= covered:
        errors.append(
            "mechanical-gates: open physical fits lack dispositions: "
            + ", ".join(sorted(required_open_instances - covered))
        )
    return errors


def validate_source_research() -> list[str]:
    """Keep the accepted research-first / purchase-last sequence machine-checkable."""
    data = json.loads(SOURCE_RESEARCH_PATH.read_text(encoding="utf-8"))
    errors: list[str] = []
    if data.get("schema_version") != 1 or data.get("stage") != "H1.1.3.3":
        errors.append("source-research: schema/stage mismatch")
    if data.get("status") != "reviewed" or data.get("current_substep") != "H1-R2.39":
        errors.append("source-research: exact current substep drifted")
    policy = data.get("policy", {})
    if policy.get("order_authorized") is not False:
        errors.append("source-research: sample order must remain unauthorized")
    if policy.get("purchase_is_last_resort") is not True:
        errors.append("source-research: purchase-last policy was lost")
    sequence = policy.get("sequence", [])
    expected = [
        ("H1.1.3.3.1", "reviewed"),
        ("H1.1.3.3.2", "reviewed"),
        ("H1.1.3.3.3", "reviewed"),
        ("H1.1.3.3.4", "not_required"),
    ]
    actual = [(row.get("id"), row.get("status")) for row in sequence]
    if actual != expected:
        errors.append("source-research: research/replacement/request/sample order drifted")
    subjects = {row.get("id"): row for row in data.get("subjects", [])}
    if set(subjects) != {"display", "nrf24", "u214"}:
        errors.append("source-research: exact H1 source subjects drifted")
    for subject_id, subject in subjects.items():
        if not subject.get("official_findings"):
            errors.append(f"source-research: {subject_id} lacks official findings")
        if not subject.get("replacement_review"):
            errors.append(f"source-research: {subject_id} lacks replacement review")
        if not subject.get("remaining_gap") or not subject.get("current_disposition"):
            errors.append(f"source-research: {subject_id} lacks disposition")
    return errors


def validate_navigation_cluster(design: dict, devices: dict, instances: dict) -> list[str]:
    """Prove that the navigation cluster contains only exact serial buttons."""
    errors: list[str] = []
    if (
        design.get("schema_version") != 1
        or design.get("stage") != "H1.3.0"
        or design.get("design_id") != "L2-NAV-5B-001-A"
        or design.get("status") != "selected"
    ):
        errors.append("navigation-cluster: schema, stage, identity or status drifted")
    if design.get("manufacturing_class") != "serial_components_only":
        errors.append("navigation-cluster: only serial components are allowed")
    component = design.get("component", {})
    if component.get("device_key") != "omron_b3s_1100p" or component.get("mpn") != "OMRON B3S-1100P":
        errors.append("navigation-cluster: exact serial button MPN drifted")
    switch = devices.get(component.get("device_key"), {})
    if component.get("body_mm") != switch.get("dimensions_mm") or component.get("quantity") != 5:
        errors.append("navigation-cluster: serial button quantity or envelope drifted")
    if "no separate cap" not in str(component.get("actuation", "")):
        errors.append("navigation-cluster: a hidden cap or custom actuator was introduced")
    if not str(component.get("manufacturer_url", "")).startswith("https://components.omron.com/"):
        errors.append("navigation-cluster: manufacturer source must remain OMRON-controlled")
    expected_instances = {
        "ui_dpad_up", "ui_dpad_down", "ui_dpad_left", "ui_dpad_right", "ui_dpad_ok"
    }
    buttons = design.get("layout", {}).get("buttons", [])
    button_by_instance = {row.get("instance"): row for row in buttons}
    if set(button_by_instance) != expected_instances or len(buttons) != 5:
        errors.append("navigation-cluster: exact five-button instance set drifted")
    selected = {item.instance: item for item in FRONT_CONTROLS if item.instance in expected_instances}
    if set(selected) != expected_instances:
        errors.append("navigation-cluster: a direction or OK is absent from the front placement")
    for instance in expected_instances:
        if instances.get(instance) != "omron_b3s_1100p":
            errors.append(f"navigation-cluster: {instance} is not the selected serial B3S-1100P")
            continue
        expected_position = [selected[instance].x, selected[instance].y]
        if button_by_instance.get(instance, {}).get("position_mm") != expected_position:
            errors.append(f"navigation-cluster: {instance} position disagrees with the renderer")
    if design.get("electrical_contract", {}).get("expander_contacts_consumed") != 5:
        errors.append("navigation-cluster: exact five-input pin budget drifted")
    cost = design.get("cost_at_quantity_100_usd", {})
    selected_unit = float(switch.get("cost", {}).get("unit_price_usd", 0))
    if not math.isclose(float(cost.get("five_b3s_1100p", -1)), 5 * selected_unit, abs_tol=1e-9):
        errors.append("navigation-cluster: five-button cost is stale")
    checks = design.get("paper_checks", {})
    control_by_instance = {item.instance: item for item in FRONT_CONTROLS}
    switch_w = float(component.get("body_mm", [0, 0, 0])[0])
    cluster_x, _, cluster_w, _ = map(float, design.get("layout", {}).get("bounding_box_mm", [0, 0, 0, 0]))
    expected_back_clearance = cluster_x - (
        control_by_instance["ui_switch_back"].x + switch_w
    )
    expected_opt_clearance = control_by_instance["ui_switch_opt"].x - (
        cluster_x + cluster_w
    )
    if not math.isclose(float(checks.get("back_clearance_mm", -1)), expected_back_clearance, abs_tol=1e-9):
        errors.append("navigation-cluster: BACK clearance disagrees with the renderer")
    if not math.isclose(float(checks.get("opt_clearance_mm", -1)), expected_opt_clearance, abs_tol=1e-9):
        errors.append("navigation-cluster: OPT clearance disagrees with the renderer")
    if checks.get("custom_mechanical_parts") != 0:
        errors.append("navigation-cluster: custom mechanical parts are forbidden")
    if not all(checks.get(field) is True for field in ("all_five_bodies_inside_board", "mounting_keepouts_clear")):
        errors.append("navigation-cluster: paper containment checks are incomplete")
    if len(design.get("h5_acceptance", [])) < 4 or "H5" not in design.get("release_boundary", ""):
        errors.append("navigation-cluster: assembled control H5 gate is incomplete")
    return errors


def validate_display_mount_design(
    design: dict, devices: dict, candidate: dict, instances: dict
) -> list[str]:
    """Keep the direct panel-to-UI ZIF and non-load-bearing mount honest."""
    errors: list[str] = []
    if design.get("schema_version") != 1 or design.get("design_id") != "L2-DISP-DIRECT-001-A":
        errors.append("display-mount: schema/design identity mismatch")
    if design.get("stage") != "H1-R2.39":
        errors.append("display-mount: exact source-research stage drifted")
    rows = design.get("components", [])
    if len(rows) != 1 or rows[0].get("instance") != "display_connector":
        errors.append("display-mount: exactly one direct connector is required")
        return errors
    connector = rows[0]
    device = devices[instances["display_connector"]]
    expected_mpn = "Hirose FH34SRJ-50S-0.5SH(50)"
    if connector.get("mpn") != expected_mpn or device.get("mpn") != expected_mpn:
        errors.append("display-mount: exact direct ZIF MPN drifted")
    if [float(value) for value in connector.get("envelope_mm", [])] != [
        float(value) for value in device.get("dimensions_mm", [])
    ]:
        errors.append("display-mount: direct ZIF envelope disagrees with device register")
    x, y = map(float, connector.get("ui_inner_position_mm", [0, 0]))
    width, height, body_z = map(float, connector.get("envelope_mm", [0, 0, 0]))
    box = (x, y, width, height)
    if x < 0 or y < 0 or x + width > BOARD_W or y + height > BOARD_H:
        errors.append("display-mount: direct ZIF leaves the UI-board projection")
    if any(hits_hole(box, hole, MIN_INTERBOARD_Z_CLEARANCE_MM) for hole in HOLES):
        errors.append("display-mount: direct ZIF enters a mounting-hole keep-out")
    ui_connector = next((item for item in UI_INNER if item.instance == "display_connector"), None)
    if ui_connector is None or (ui_connector.x, ui_connector.y) != (x, y):
        errors.append("display-mount: ZIF coordinate disagrees with UI-inner placement")
    for item in UI_INNER:
        if item.instance == "display_connector":
            continue
        if overlaps(box, (item.x, item.y, *placement_size(item, devices, instances))):
            errors.append(f"display-mount: direct ZIF conflicts with {item.instance}")
    stack = design.get("stack", {})
    if not math.isclose(
        body_z, float(stack.get("connector_height_from_ui_inner_mm", -1)), abs_tol=1e-9
    ):
        errors.append("display-mount: stored connector height is stale")
    if body_z + float(stack.get("minimum_reserved_clearance_mm", 0)) > INTERBOARD_GAP_MM:
        errors.append("display-mount: direct ZIF exceeds the interboard gap")
    for clearance, rf_item in display_mount_opposing_clearance_pairs(design, devices, instances):
        if clearance < MIN_INTERBOARD_Z_CLEARANCE_MM:
            errors.append(
                f"display-mount: direct ZIF opposite {rf_item.instance} leaves only "
                f"{clearance:.2f} mm, below the {MIN_INTERBOARD_Z_CLEARANCE_MM:.1f}-mm minimum"
            )
    retention = design.get("mechanical_retention", {})
    if retention.get("connector_is_load_bearing") is not False:
        errors.append("display-mount: ZIF must be explicitly non-load-bearing")
    for field in ("panel_support", "primary_retention", "secondary_retention", "flex_strain_relief", "service_rule"):
        if not retention.get(field):
            errors.append(f"display-mount: mechanical retention lacks {field}")
    physical_parts = {
        row.get("id"): row for row in retention.get("physical_realization", [])
    }
    expected_physical_parts = {
        "ui_pcb_display_bed": 1,
        "display_psa_rectangle": 1,
        "display_alignment_silkscreen": 1,
        "fpc_bend_guide": 1,
    }
    if {
        part_id: physical_parts.get(part_id, {}).get("quantity")
        for part_id in expected_physical_parts
    } != expected_physical_parts:
        errors.append("display-mount: physical retention implementation is incomplete")
    if not retention.get("structural_load_path", "").endswith("never through the FPC or ZIF"):
        errors.append("display-mount: structural load path must terminate outside the FPC and ZIF")
    fpc_route = retention.get("fpc_route_side_section", {})
    if (
        fpc_route.get("tail_under_psa") is not False
        or fpc_route.get("tail_bears_on_bare_pcb_edge") is not False
        or fpc_route.get("hard_crease_allowed") is not False
        or fpc_route.get("component_bearing_fpc_compressed") is not False
        or fpc_route.get("twist_allowed") is not False
        or fpc_route.get("fold_count") != 1
        or fpc_route.get("minimum_bend_radius_mm") is not None
        or "H5" not in fpc_route.get("bend_radius_gate", "")
    ):
        errors.append("display-mount: side-section FPC route is not fail-closed")
    if not all(
        math.isclose(float(fpc_route.get(field, -1)), expected, abs_tol=1e-9)
        for field, expected in (
            ("pcb_thickness_mm", 1.6),
            ("drawing_stock_pad_envelope_mm", 1.016),
            ("zif_height_mm", body_z),
            ("contact_stiffener_thickness_mm", 0.3),
            ("contact_tail_width_mm", 25.5),
            ("pcb_slot_width_mm", 27.0),
            ("pcb_slot_height_mm", 1.2),
        )
    ):
        errors.append("display-mount: side-section dimensions drifted")
    if fpc_route.get("stock_pad_release_rule") != "exact stock pad thickness >= measured folded FPC maximum stack + 0.20 mm":
        errors.append("display-mount: folded-FPC stock-pad clearance rule drifted")
    stock_rectangle = fpc_route.get("stock_psa_rectangle_size_mm", [])
    support_fraction = (
        float(stock_rectangle[0]) * float(stock_rectangle[1]) / (DISPLAY_W * DISPLAY_H)
        if len(stock_rectangle) == 2
        else 0
    )
    if (
        fpc_route.get("separate_upper_tape_fitted") is not False
        or fpc_route.get("upper_support_part_fitted") is not False
        or fpc_route.get("custom_die_cut_required") is not False
        or fpc_route.get("external_converter_order_allowed") is not False
        or fpc_route.get("adhesive_piece_count") != 1
        or fpc_route.get("alignment_silkscreen_datum_count") != 2
        or not math.isclose(float(fpc_route.get("supported_panel_area_fraction", 0)), support_fraction, abs_tol=0.001)
        or support_fraction < 0.50
        or stock_rectangle != [50.8, 50.8]
        or len(fpc_route.get("stock_psa_rectangle_position_mm", [])) != 2
        or not math.isclose(float(fpc_route["stock_psa_rectangle_position_mm"][0]), DISPLAY_X + 2.87, abs_tol=1e-9)
        or not math.isclose(float(fpc_route["stock_psa_rectangle_position_mm"][1]), 44.46, abs_tol=1e-9)
    ):
        errors.append("display-mount: stocked rectangular PSA support geometry drifted")
    manufacturing = design.get("manufacturing_route", {})
    if (
        "stocked 50.8 x 50.8-mm" not in manufacturing.get("baseline", "")
        or manufacturing.get("wait_for_custom_service_answer") is not False
        or manufacturing.get("external_converter_order_allowed") is not False
        or manufacturing.get("custom_pcba_die_cut_status") != "not publicly documented and the earlier support request remains unanswered"
    ):
        errors.append("display-mount: non-blocking stock-rectangle manufacturing route drifted")
    pad_candidate = manufacturing.get("primary_stock_pad_candidate", {})
    if (
        pad_candidate.get("manufacturer") != "3M (TC)"
        or pad_candidate.get("mpn") != "4910SQ-2(5)"
        or pad_candidate.get("distributor_part") != "1067-4910SQ-2(5)-ND"
        or pad_candidate.get("form_mm") != [50.8, 50.8, 1.016]
        or not math.isclose(float(pad_candidate.get("minimum_spec_thickness_mm", -1)), 0.914, abs_tol=1e-9)
        or not math.isclose(float(pad_candidate.get("maximum_allowed_folded_fpc_stack_mm", -1)), 0.714, abs_tol=1e-9)
        or "customer-supplied J4-F" not in pad_candidate.get("jlcpcb_standard_pcba_status_on_2026_09_01", "")
    ):
        errors.append("display-mount: traceable stock PSA qualification candidate drifted")
    slot_x, slot_y = map(float, fpc_route.get("pcb_slot_position_mm", [-1, -1]))
    slot_w = float(fpc_route.get("pcb_slot_width_mm", -1))
    slot_h = float(fpc_route.get("pcb_slot_height_mm", -1))
    tail_w = float(fpc_route.get("contact_tail_width_mm", -1))
    tail_tol = float(fpc_route.get("contact_tail_width_tolerance_mm", -1))
    nominal_lateral = (slot_w - tail_w) / 2
    worst_lateral = (slot_w - tail_w - tail_tol) / 2
    paper_checks = design.get("paper_checks", {})
    if not math.isclose(
        float(paper_checks.get("nominal_slot_lateral_clearance_each_side_mm", -1)),
        nominal_lateral,
        abs_tol=1e-9,
    ) or not math.isclose(
        float(paper_checks.get("worst_case_slot_lateral_clearance_each_side_mm", -1)),
        worst_lateral,
        abs_tol=1e-9,
    ):
        errors.append("display-mount: FPC tongue/slot lateral clearance drifted")
    if worst_lateral < 0.5:
        errors.append("display-mount: worst-case FPC tongue/slot lateral clearance is below 0.5 mm")
    if not math.isclose(slot_x, 26.5, abs_tol=1e-9) or not math.isclose(slot_y, 23.0, abs_tol=1e-9):
        errors.append("display-mount: slack-qualified FPC slot position drifted")
    if not math.isclose(x, slot_x, abs_tol=1e-9) or not math.isclose(y, 25.0, abs_tol=1e-9):
        errors.append("display-mount: slack-qualified direct-ZIF position drifted")
    if y - (slot_y + slot_h) < 0.7:
        errors.append("display-mount: FPC slot-to-ZIF mouth corridor is below 0.7 mm")
    if not (
        DISPLAY_X <= slot_x
        and slot_x + slot_w <= DISPLAY_X + DISPLAY_W
        and DISPLAY_Y <= slot_y
        and slot_y + slot_h <= DISPLAY_Y + DISPLAY_H
    ):
        errors.append("display-mount: rounded FPC tongue slot escaped the panel footprint")
    h1_placement = json.loads(H1_R2_PLACEMENT_PATH.read_text(encoding="utf-8"))
    ufl_ids = {
        "s3_rf_board_connector_r2", "c5_rf_board_connector_r2",
        "nrf0_rf_board_connector_r2", "nrf1_rf_board_connector_r2",
        "nrf2_rf_board_connector_r2",
    }
    ufl_rows = [row for row in h1_placement.get("placements", []) if row.get("id") in ufl_ids]
    if {row.get("id") for row in ufl_rows} != ufl_ids:
        errors.append("display-mount: five board U.FL bodies are not registered")
    else:
        ufl_max_y = max(float(row["world_xy_mm"][1]) + float(row["size_mm"][1]) for row in ufl_rows)
        ufl_gap = slot_y - ufl_max_y
        if not math.isclose(
            float(paper_checks.get("minimum_slot_to_existing_ufl_body_gap_mm", -1)),
            ufl_gap,
            abs_tol=1e-9,
        ) or ufl_gap < 0.7:
            errors.append("display-mount: FPC slot/U.FL separation drifted")
    source_tail = float(fpc_route.get("source_tail_length_from_panel_edge_to_tip_mm", -1))
    source_tol = float(fpc_route.get("source_tail_length_tolerance_mm", -1))
    minimum_tail = source_tail - source_tol
    panel_edge_y = float(fpc_route.get("panel_tail_exit_edge_y_mm", -1))
    connector_full_depth_y = y + height
    panel_to_connector = connector_full_depth_y - panel_edge_y
    raw_reserve = minimum_tail - panel_to_connector
    protected_slack = float(fpc_route.get("minimum_relaxed_service_slack_mm", -1))
    maximum_route = minimum_tail - protected_slack
    bend_budget = raw_reserve - protected_slack
    calculated_slack = {
        "minimum_source_tail_length_mm": minimum_tail,
        "connector_full_depth_reach_y_mm": connector_full_depth_y,
        "minimum_raw_length_reserve_mm": raw_reserve,
        "maximum_measured_route_to_contact_stop_mm": maximum_route,
        "bend_insertion_and_tolerance_budget_mm": bend_budget,
    }
    if any(
        not math.isclose(float(fpc_route.get(field, -1)), expected, abs_tol=1e-9)
        for field, expected in calculated_slack.items()
    ):
        errors.append("display-mount: source-tail slack budget drifted")
    paper_slack = {
        "minimum_tail_length_mm": minimum_tail,
        "panel_edge_to_connector_full_depth_mm": panel_to_connector,
        "minimum_raw_length_reserve_mm": raw_reserve,
        "minimum_relaxed_service_slack_mm": protected_slack,
        "maximum_measured_route_to_contact_stop_mm": maximum_route,
        "bend_insertion_and_tolerance_budget_mm": bend_budget,
    }
    if any(
        not math.isclose(float(paper_checks.get(field, -1)), expected, abs_tol=1e-9)
        for field, expected in paper_slack.items()
    ):
        errors.append("display-mount: paper tail-slack audit disagrees with geometry")
    if raw_reserve < 10.0 or protected_slack < 5.0 or bend_budget < 5.0:
        errors.append("display-mount: protected FPC slack or bend budget is insufficient")
    if "<= 24.66 mm" not in fpc_route.get("slack_release_rule", ""):
        errors.append("display-mount: received-panel neutral-axis route gate is missing")
    div_reference = retention.get("esp32_div_v2_reference", {})
    if div_reference.get("retention_evidence_status") != "unknown_from_public_sources":
        errors.append("display-mount: DIV retention must remain explicitly unproven")
    if "four empty 1.2-mm holes" not in div_reference.get("in_plane_location", ""):
        errors.append("display-mount: DIV reference must preserve the four observed empty holes")
    if "18-contact" not in div_reference.get("electrical_connection", ""):
        errors.append("display-mount: DIV reference must preserve the direct-soldered 18-contact flex")
    if "non-load-bearing ZIF" not in div_reference.get("leshy2_adoption_rule", ""):
        errors.append("display-mount: DIV comparison must not make the Leshy2 ZIF load-bearing")
    orientation = design.get("orientation", {})
    if orientation.get("fpc_exit_direction_board_axis") != "-Y":
        errors.append("display-mount: panel FPC must exit toward board -Y / the antenna edge")
    if "stop-work" not in orientation.get("factory_orientation_check", ""):
        errors.append("display-mount: owner orientation check must fail closed before PSA pressing")
    if orientation.get("connector_contact_orientation") != "top and bottom contact":
        errors.append("display-mount: exact FH34SRJ dual-contact orientation was lost")
    if orientation.get("tail_pin_1_world_side_after_rotation_and_fold") != "board left / world x-min":
        errors.append("display-mount: folded tail pin 1 no longer lands at world x-min")
    if orientation.get("connector_pin_1_world_side") != "board right / world x-max":
        errors.append("display-mount: manufacturer connector pin 1 must mate tail pin 50 at world x-max")
    if orientation.get("tail_pin_50_world_side_after_rotation_and_fold") != "board right / world x-max":
        errors.append("display-mount: folded tail pin 50 no longer lands at world x-max")
    if orientation.get("connector_pin_50_world_side") != "board left / world x-min":
        errors.append("display-mount: manufacturer connector pin 50 must mate tail pin 1 at world x-min")
    if paper_checks.get("pin_order_and_contact_face_checked") is not True:
        errors.append("display-mount: pin-order/contact-face paper check is not closed")
    electrical = design.get("electrical", {})
    if electrical.get("owner_contract") != {
        "display_bus_owner": "s3",
        "touch_host_owner": "s3",
        "c5_display_or_touch_connection": "none",
    }:
        errors.append("display-mount: display and touch must remain exclusively S3-owned")
    panel_map = electrical.get("panel_pin_map", {})
    expected_mating_map = {str(pin): str(51 - pin) for pin in range(1, 51)}
    if electrical.get("panel_to_connector_pin_map") != expected_mating_map:
        errors.append("display-mount: panel-to-FH34 mating map must be the complete 1..50 -> 50..1 bijection")
    if set(panel_map) != {str(pin) for pin in range(1, 51)}:
        errors.append("display-mount: exact 50-contact panel map is incomplete")
    if int(electrical.get("panel_position_count", 0)) != 50:
        errors.append("display-mount: panel position count drifted")
    if electrical.get("selected_mode") != "ILI9488 8080 8-bit with IM2/IM1/IM0 = 0/1/1":
        errors.append("display-mount: selected ILI9488 i8080 strap drifted")
    expected_mode_straps = {"7": "LCD_IM0_HIGH", "8": "LCD_IM1_HIGH", "9": "LCD_IM2_LOW"}
    for pin, expected in expected_mode_straps.items():
        if panel_map.get(pin) != expected:
            errors.append(f"display-mount: panel pin {pin} mode strap drifted")
    if any(value.startswith("MAIN_") for value in panel_map.values()):
        errors.append("display-mount: obsolete intermediate 40-contact map remains")
    if "H5" not in design.get("release_boundary", ""):
        errors.append("display-mount: received-tail fit must remain an H5 gate")
    return errors


def validate_assembly_coordinate_model(
    model: dict, devices: dict, instances: dict, display_mount_design: dict
) -> list[str]:
    """Prove that every view shares one X/Y/Z datum and board transformation."""
    errors: list[str] = []
    if (
        model.get("schema_version") != 1
        or model.get("model_id") != "L2-ASM-COORD-001-A"
        or model.get("stage") != "H1-R2.39"
        or model.get("status") != "reviewed"
    ):
        errors.append("coordinate-model: schema, identity, stage or review status drifted")
    if [float(value) for value in model.get("board_outline_mm", [])] != [BOARD_W, BOARD_H]:
        errors.append("coordinate-model: board outline disagrees with the renderers")
    holes = model.get("mounting_holes", {})
    if float(holes.get("diameter_mm", 0)) != MOUNT_HOLE_D:
        errors.append("coordinate-model: mounting-hole diameter drifted")
    if float(holes.get("head_keepout_radius_mm", 0)) != MOUNT_KEEPOUT_R:
        errors.append("coordinate-model: mounting keep-out drifted")
    if [tuple(map(float, row)) for row in holes.get("world_xy", [])] != list(HOLES):
        errors.append("coordinate-model: mounting axes disagree with every board view")

    stack = model.get("stack", {})
    display_depth = float(devices[instances["display"]]["dimensions_mm"][2])
    expected_stack = {
        "display_front_z": 0.0,
        "display_depth_mm": display_depth,
        "ui_outer_face_z": display_depth,
        "ui_pcb_thickness_mm": 1.6,
        "ui_inner_face_z": display_depth + 1.6,
        "interboard_gap_mm": INTERBOARD_GAP_MM,
        "rf_inner_face_z": display_depth + 1.6 + INTERBOARD_GAP_MM,
        "rf_pcb_thickness_mm": 1.6,
        "rf_outer_face_z": display_depth + 1.6 + INTERBOARD_GAP_MM + 1.6,
        "selected_base_stack_depth_mm": display_depth + 1.6 + INTERBOARD_GAP_MM + 1.6,
    }
    for field, expected in expected_stack.items():
        if not math.isclose(float(stack.get(field, -999)), expected, abs_tol=1e-9):
            errors.append(f"coordinate-model: {field} is stale (expected {expected:.3f})")

    planes = model.get("antenna_planes", {})
    front_centre = float(stack.get("ui_outer_face_z", 0)) - RF_BARREL_D / 2
    rear_centre = float(stack.get("rf_outer_face_z", 0)) + RF_BARREL_D / 2
    if not math.isclose(float(planes.get("front_bank_centre_z", -1)), front_centre, abs_tol=0.001):
        errors.append("coordinate-model: front antenna centre plane drifted")
    if not math.isclose(float(planes.get("rear_bank_centre_z", -1)), rear_centre, abs_tol=0.001):
        errors.append("coordinate-model: rear antenna centre plane drifted")
    if not math.isclose(
        float(planes.get("centre_plane_separation_mm", -1)),
        rear_centre - front_centre,
        abs_tol=0.001,
    ):
        errors.append("coordinate-model: antenna centre-plane separation drifted")

    zones = model.get("longitudinal_zones", {})
    u214_y = list(map(float, zones.get("u214_cap_y_mm", [])))
    battery_y = list(map(float, zones.get("battery_holder_y_mm", [])))
    if (
        len(u214_y) != 2
        or any(not math.isclose(actual, expected, abs_tol=1e-9) for actual, expected in zip(u214_y, [U214_Y, U214_Y + U214_H]))
        or battery_y != [PACK_HOLDER_Y, PACK_HOLDER_Y + PACK_HOLDER_H]
    ):
        errors.append("coordinate-model: U214 or battery Y zone drifted")
    elif u214_y[1] + U214_CLEARANCE > battery_y[0]:
        errors.append("coordinate-model: U214 and battery longitudinal zones overlap")

    envelopes = model.get("accessory_envelopes", {})
    direct_zif = envelopes.get("display_direct_zif", {})
    connector = display_mount_design["components"][0]
    connector_x, connector_y = map(float, connector["ui_inner_position_mm"])
    connector_w, connector_h, connector_z = map(float, connector["envelope_mm"])
    expected_connector = {
        "x_mm": [connector_x, connector_x + connector_w],
        "y_mm": [connector_y, connector_y + connector_h],
        "z_mm": [
            float(stack.get("ui_inner_face_z", 0)),
            float(stack.get("ui_inner_face_z", 0)) + connector_z,
        ],
    }
    for axis, expected in expected_connector.items():
        if [float(value) for value in direct_zif.get(axis, [])] != expected:
            errors.append(f"coordinate-model: direct display ZIF {axis} envelope drifted")
    if expected_connector["z_mm"][1] + MIN_INTERBOARD_Z_CLEARANCE_MM > float(stack.get("rf_inner_face_z", 0)):
        errors.append("coordinate-model: direct display ZIF violates the unified Z channel")

    u214 = envelopes.get("u214", {})
    if [float(value) for value in u214.get("x_mm", [])] != [U214_X, U214_X + U214_W]:
        errors.append("coordinate-model: U214 X envelope drifted")
    if (
        len(u214.get("y_mm", [])) != 2
        or any(
            not math.isclose(float(actual), expected, abs_tol=1e-9)
            for actual, expected in zip(u214.get("y_mm", []), [U214_Y, U214_Y + U214_H])
        )
    ):
        errors.append("coordinate-model: U214 Y envelope drifted")
    if not model.get("enclosure_reference", {}).get("not_yet_locked"):
        errors.append("coordinate-model: enclosure-open boundary must remain explicit")
    return errors
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
