anton-vinogradov/esp32-leshy2/hardware/layout/h6_r2_placement_intent.py

#!/usr/bin/env python3
"""Independent product-intent checks, not a comparison to the placement freeze.

These requirements come from the exterior arrangement requested by the owner.
Changing a frozen coordinate or drawing cannot make a misplaced part pass.
This finite audit does not qualify component Z envelopes or factory assembly.
"""
from __future__ import annotations

import argparse
import hashlib
import importlib.util
import json
import math
from pathlib import Path

ROOT = Path(__file__).resolve().parents[2]
DEST = ROOT / "hardware/layout/generated/H6-R2-placement-intent.json"
PROJECTS = ("LESHY2-UI-R2", "LESHY2-RF-R2")
PLACEMENT_CONTRACT = "hardware/layout/h6-r2-placement-contract.json"
LED_ROWS = (("D9", "D1", "D6", "D7", "D8"), ("D2", "D10", "D5", "D3", "D4"))
LED_COLUMNS_MM = (8.4, 24.2, 40.0, 55.8, 71.6)


def finite_vector(value, length):
    return (isinstance(value, (list, tuple)) and len(value) == length
            and all(type(v) in (int, float) and math.isfinite(v) for v in value))


def native_bottom_edges(board, pcbnew):
    """Observe the finite UI bottom contour directly, without placement inputs.

    The corner arcs extend beyond X2..78 and are outside this notch feature.
    Start/mid/end points retain the actual native arc instead of its bbox.
    """
    result = []
    point = lambda p: [round(pcbnew.ToMM(p.x), 6), round(pcbnew.ToMM(p.y), 6)]
    for item in board.GetDrawings():
        if not isinstance(item, pcbnew.PCB_SHAPE) or item.GetLayer() != pcbnew.Edge_Cuts:
            continue
        if item.GetShape() == pcbnew.SHAPE_T_SEGMENT:
            kind, points = "line", [point(item.GetStart()), point(item.GetEnd())]
        elif item.GetShape() == pcbnew.SHAPE_T_ARC:
            kind, points = "arc", [point(item.GetStart()), point(item.GetArcMid()), point(item.GetEnd())]
        else:
            continue
        if all(1.999 <= x <= 78.001 and 147.999 <= y <= 150.001 for x, y in points):
            result.append([kind, *points])
    return sorted(result)


def checked_native_notch(edges):
    """Independent nominal 10x1.2/R0.6 opening; not a tolerance/fit proof."""
    expected = [
        ["line", [78, 150], [66.43, 150]],
        ["line", [66.43, 150], [66.43, 149.4]],
        ["arc", [66.43, 149.4], [66.254264, 148.975736], [65.83, 148.8]],
        ["line", [65.83, 148.8], [57.03, 148.8]],
        ["arc", [57.03, 148.8], [56.605736, 148.975736], [56.43, 149.4]],
        ["line", [56.43, 149.4], [56.43, 150]],
        ["line", [56.43, 150], [2, 150]],
    ]
    def matches(a, b):
        if len(a) != len(b) or a[0] != b[0]:
            return False
        return any(all(abs(x-y) <= .002 for p, q in zip(a[1:], points)
                       for x, y in zip(p, q))
                   for points in (b[1:], b[1:][::-1]))
    # Cardinality plus a bijection rejects duplicate, missing and closing edges.
    remaining = list(edges)
    for wanted in expected:
        hits = [i for i, observed in enumerate(remaining) if matches(observed, wanted)]
        if len(hits) != 1:
            return {"pass": False, "observed_edges": edges}
        remaining.pop(hits[0])
    if remaining:
        return {"pass": False, "observed_edges": edges}
    floor = next(row for row in edges if row[0] == "line"
                 and all(abs(p[1]-148.8) <= .002 for p in row[1:]))
    return {"pass": True, "axis_x_mm": sum(p[0] for p in floor[1:])/2,
            "floor_y_mm": sum(p[1] for p in floor[1:])/2,
            "observed_edges": edges}


def native_microphone_labels(board, pcbnew):
    """Read actual board text, including hidden/wrong-face/duplicate labels."""
    result = []
    point = lambda p: [round(pcbnew.ToMM(p.x), 6), round(pcbnew.ToMM(p.y), 6)]
    for item in board.GetDrawings():
        if not isinstance(item, pcbnew.PCB_TEXT) or item.GetText() not in {"MIC", "MICROPHONE"}:
            continue
        result.append({"text": item.GetText(), "at_mm": point(item.GetPosition()),
                       "layer": ("F.Silkscreen" if item.GetLayer() == pcbnew.F_SilkS else
                                 "B.Silkscreen" if item.GetLayer() == pcbnew.B_SilkS else
                                 board.GetLayerName(item.GetLayer())),
                       "size_mm": point(item.GetTextSize()),
                       "thickness_mm": pcbnew.ToMM(item.GetTextThickness()),
                       "angle_deg": item.GetTextAngleDegrees(),
                       "visible": item.IsVisible(), "mirrored": item.IsMirrored(),
                       "default_stroke_font": item.GetFont() is None,
                       "bold": item.IsBold(), "italic": item.IsItalic(),
                       "horizontal_justify": int(item.GetHorizJustify()),
                       "vertical_justify": int(item.GetVertJustify())})
    return result


def exact_microphone_label(row, layer, at_mm, mirrored, tolerance=.002):
    """Finite native MIC presentation; malformed fields fail without defaults."""
    def near(value, expected):
        return (isinstance(value, (int, float)) and not isinstance(value, bool)
                and math.isfinite(value) and abs(value-expected) <= tolerance)

    def pair(value, expected):
        return (isinstance(value, (list, tuple)) and len(value) == 2
                and all(near(v, e) for v, e in zip(value, expected)))

    if not isinstance(row, dict):
        return False
    angle = row.get("angle_deg")
    return (row.get("text") == "MIC" and row.get("layer") == layer
            and pair(row.get("at_mm"), at_mm) and pair(row.get("size_mm"), [1., 1.])
            and near(row.get("thickness_mm"), .15)
            and isinstance(angle, (int, float)) and not isinstance(angle, bool)
            and math.isfinite(angle) and near(angle % 360, 0)
            and row.get("visible") is True and row.get("mirrored") is mirrored
            and row.get("default_stroke_font") is True
            and row.get("bold") is False and row.get("italic") is False
            and type(row.get("horizontal_justify")) is int
            and type(row.get("vertical_justify")) is int
            and row.get("horizontal_justify") == row.get("vertical_justify") == 0)


def native_snapshot(root=ROOT):
    import pcbnew
    result = {"boards": {}, "sources": {}, "assembly_registration": {}, "bottom_edges": {},
              "microphone_labels": {}}
    script = Path(__file__).resolve()
    result["sources"][str(script.relative_to(root))] = hashlib.sha256(script.read_bytes()).hexdigest()
    helper = root / "hardware/layout/h6_r2_speaker_fit.py"
    speaker_json = root / "hardware/layout/h6-r2-speaker-body.json"
    contract_json = root / PLACEMENT_CONTRACT
    for path in (helper, speaker_json, contract_json):
        result["sources"][str(path.relative_to(root))] = hashlib.sha256(path.read_bytes()).hexdigest()
    # The unfitted panel is a controlled nominal envelope, not a PCB footprint.
    result["display_panel_bbox_mm"] = json.loads(contract_json.read_text())["mechanical"]["display_bed"]["panel_bbox_mm"]
    spec = importlib.util.spec_from_file_location("intent_speaker", helper)
    speaker = importlib.util.module_from_spec(spec)
    spec.loader.exec_module(speaker)
    speaker_body = json.loads(speaker_json.read_text())
    for project in PROJECTS:
        path = root / f"hardware/ecad/kicad/{project}/{project}.kicad_pcb"
        result["sources"][str(path.relative_to(root))] = hashlib.sha256(path.read_bytes()).hexdigest()
        board = pcbnew.LoadBoard(str(path))
        result["microphone_labels"][project] = native_microphone_labels(board, pcbnew)
        if project == PROJECTS[0]:
            result["bottom_edges"][project] = native_bottom_edges(board, pcbnew)
        result["assembly_registration"][project] = speaker.check_native_speaker_geometry(
            board, project, pcbnew, speaker_body)
        rows = {}
        for fp in board.GetFootprints():
            reference = fp.GetReference()
            if reference in rows:
                raise ValueError(f"duplicate {project} {reference}")
            pads = list(fp.Pads())
            point = lambda p: [round(pcbnew.ToMM(p.x), 6), round(pcbnew.ToMM(p.y), 6)]
            xy = []
            for graphic in fp.GraphicalItems():
                if isinstance(graphic, pcbnew.PCB_SHAPE) and graphic.GetLayer() in (pcbnew.F_Fab, pcbnew.B_Fab):
                    bounds = graphic.GetBoundingBox()
                    xy += [point(bounds.GetOrigin()), point(bounds.GetEnd())]
            body = ([min(p[0] for p in xy), min(p[1] for p in xy),
                     max(p[0] for p in xy), max(p[1] for p in xy)] if xy else None)
            contacts = [p for p in pads if p.GetNumber() in ("1", "2", "3", "4")]
            actuator = ([sum(pcbnew.ToMM(p.GetPosition().x) for p in contacts)/4,
                         sum(pcbnew.ToMM(p.GetPosition().y) for p in contacts)/4]
                        if len(contacts) == 4 and "B3S-1100P" in str(fp.GetFPID().GetLibItemName()) else None)
            rows[reference] = {"footprint": str(fp.GetFPID().GetLibNickname()) + ":" + str(fp.GetFPID().GetLibItemName()),
                               "value": fp.GetValue(),
                               "side": "B.Cu" if fp.IsFlipped() else "F.Cu",
                               "anchor_mm": point(fp.GetPosition()),
                               "rotation_deg": fp.GetOrientationDegrees(),
                               "fab_stroke_bounds_mm": body, "actuator_mm": actuator,
                               "pad1_nets": sorted({p.GetNetname() for p in pads if p.GetNumber() == "1"})}
        result["boards"][project] = rows
    return result


def evaluate(snapshot):
    checks = []

    def check(name, condition, observed):
        checks.append({"requirement": name, "pass": bool(condition), "observed": observed})

    ui = snapshot["boards"][PROJECTS[0]]
    rf = snapshot["boards"][PROJECTS[1]]
    assembly = snapshot.get("assembly_registration", {}).get(PROJECTS[0], {})
    check("speaker body registered on UI inner face, not confused with RF wire termination",
          assembly.get("status") == "pass_scoped_native_registration"
          and assembly.get("observed_count") == assembly.get("required_count") == 5,
          assembly)
    width, height, tol = 80.0, 150.0, 0.002
    near = lambda a, b: abs(a-b) <= tol
    leds = [[ui.get(ref, {}) for ref in refs] for refs in LED_ROWS]
    aligned = all(
        finite_vector(row.get("anchor_mm"), 2)
        and row.get("side") == "F.Cu"
        and finite_vector([row.get("rotation_deg")], 1)
        and near(row["rotation_deg"] % 360, 0)
        and near(row["anchor_mm"][0], x)
        for group in leds for row, x in zip(group, LED_COLUMNS_MM))
    if aligned:
        upper_y, lower_y = (group[0]["anchor_mm"][1] for group in leds)
        aligned = (all(near(row["anchor_mm"][1], group[0]["anchor_mm"][1])
                       for group in leds for row in group)
                   and upper_y < lower_y and near(lower_y, 111.4))
    check("ten front indicator LEDs retain aligned rows and fixed function columns",
          aligned, {ref: ui.get(ref) for refs in LED_ROWS for ref in refs})
    panel = snapshot.get("display_panel_bbox_mm")
    # Independent accepted panel datum; changing a frozen LED Y or shrinking
    # the panel source cannot waive clearance. No exact upper-row Y is required.
    panel_valid = (isinstance(panel, dict) and set(panel) == {"x", "y"}
                   and finite_vector(panel["x"], 2) and finite_vector(panel["y"], 2)
                   and all(near(v, expected) for v, expected in
                           zip([*panel["x"], *panel["y"]], [11.73, 68.27, 19., 103.96])))
    bodies = {ref: ui.get(ref, {}).get("fab_stroke_bounds_mm")
              for refs in LED_ROWS for ref in refs}
    bodies_valid = all(finite_vector(body, 4) and body[0] < body[2] and body[1] < body[3]
                       for body in bodies.values())
    overlapping, gaps = [], {}
    if panel_valid and bodies_valid:
        overlapping = [ref for ref in LED_ROWS[0]
                       if bodies[ref][0] < panel["x"][1] and bodies[ref][2] > panel["x"][0]]
        gaps = {ref: round(bodies[ref][1] - panel["y"][1], 6) for ref in overlapping}
    check("three middle upper LEDs clear nominal display panel by >=1.4mm; not panel stops",
          panel_valid and bodies_valid and overlapping == ["D1", "D6", "D7"]
          and all(gap >= 1.4 for gap in gaps.values())
          and max(bodies[ref][3] for ref in LED_ROWS[0]) < min(bodies[ref][1] for ref in LED_ROWS[1]),
          {"panel_source": PLACEMENT_CONTRACT + "#/mechanical/display_bed/panel_bbox_mm",
           "nominal_panel_bbox_mm": panel, "native_fab_stroke_bounds_mm": bodies,
           "overlapping_upper_refs": overlapping, "nominal_clearances_mm": gaps,
           "minimum_nominal_clearance_mm": 1.4,
           "leds_are_panel_stops": False, "assembly_tolerances_qualified": False})
    holder, encoder, ptt, jack = (rf[r] for r in ("BT1", "SW3", "SW4", "U83"))
    check("holder centered on rear PCB, not shifted to clear another part",
          holder["side"] == "F.Cu" and near(holder["anchor_mm"][0], width/2)
          and near(holder["anchor_mm"][1], 85)
          and near(holder["rotation_deg"] % 180, 90), holder)
    body = holder["fab_stroke_bounds_mm"]
    check("holder drawing is the centered real body, not its 86mm land reserve",
          body is not None and near((body[0]+body[2])/2, width/2)
          and near((body[1]+body[3])/2, 85)
          and abs((body[2]-body[0])-39.78) < .16
          and abs((body[3]-body[1])-77.06) < .16, body)
    ntcs = [rf[r]["anchor_mm"] for r in ("R33", "R34")]
    check("two outward NTCs follow the centered cell axes",
          all(rf[r]["side"] == "F.Cu" for r in ("R33", "R34"))
          and near((ntcs[0][0]+ntcs[1][0])/2, width/2)
          and all(near(p[1], holder["anchor_mm"][1]) for p in ntcs)
          and near(ntcs[1][0]-ntcs[0][0], 19.1), ntcs)
    check("encoder on LEFT when looking at the exterior rear, antennas up",
          encoder["side"] == "F.Cu" and 0 < encoder["anchor_mm"][0] < width/4, encoder)
    # Owner's 2026-09-13 request: move the existing encoder directly below Cap.
    # This independent nominal envelope must not follow an accidental frozen Y.
    # A 15-mm knob is a design envelope, not a qualified part/body tolerance.
    knob_to_cap = encoder["anchor_mm"][1] - 7.5 - 41.02
    knob_to_holder = 20.05 - encoder["anchor_mm"][0] - 7.5
    check("encoder nominal 15mm knob directly below Cap with >=5mm plan gap",
          encoder["side"] == "F.Cu" and 5 <= knob_to_cap <= 8
          and knob_to_holder >= 3,
          {"knob_to_cap_mm": knob_to_cap, "knob_to_holder_mm": knob_to_holder,
           "assembled_access_qualified": False})
    check("PTT on RIGHT when looking at the exterior rear, antennas up",
          ptt["side"] == "F.Cu" and ptt["actuator_mm"] is not None
          and ptt["actuator_mm"][0] > width*3/4, ptt)
    check("headset jack body BETWEEN PCBs, with mouth toward left rear edge",
          jack["side"] == "B.Cu" and near(jack["rotation_deg"] % 360, 0)
          and 0 < jack["anchor_mm"][0] < 2, jack)
    mic = rf.get("MK1")
    # Original intent is an internal RF capsule at the bottom enclosure exit,
    # not a new rear-normal acoustic port. Primary maximum diameter is 4.2 mm.
    # This finite XY/side screen does not prove the remaining acoustic channel.
    mic_rim_gap = height-mic["anchor_mm"][1]-2.1 if mic is not None else None
    check("exact microphone inside RF at the lower-edge acoustic corridor",
          mic is not None and mic.get("footprint") == "Leshy2:CMEJ-0413-42-SMT-TR"
          and mic.get("value") == "Same Sky CMEJ-0413-42-SMT-TR"
          and mic.get("side") == "B.Cu" and near(mic["rotation_deg"] % 360, 0)
          and abs(mic["anchor_mm"][0]-47.0) <= .25+1e-9
          and .3-1e-9 <= mic_rim_gap <= .8+1e-9,
          {"pose": mic, "maximum_body_diameter_mm": 4.2,
           "maximum_body_rim_to_bottom_mm": mic_rim_gap,
           "scope": "RF-inner top port and lower-edge corridor; actual bottom acoustic path remains unqualified"})
    mic_labels = snapshot.get("microphone_labels", {})
    ui_mic_labels = mic_labels.get(PROJECTS[0], [])
    label = ui_mic_labels[0] if len(ui_mic_labels) == 1 else None
    check("one readable UI front MIC label follows the RF microphone through the assembly transform",
          mic is not None and exact_microphone_label(
              label, "F.Silkscreen", [width-mic["anchor_mm"][0], 148.9], False, tol),
          {"ui_labels": ui_mic_labels, "rf_labels": mic_labels.get(PROJECTS[1], []),
           "expected_ui_x_mm": width-mic["anchor_mm"][0] if mic is not None else None,
           "reference": "RF:MK1", "role": "cross_board_acoustic",
           "meaning": "MIC abbreviates the RF microphone at bottom enclosure access; it does not claim a downward capsule-port normal"})
    rf_mic_labels = mic_labels.get(PROJECTS[1], [])
    # The optional inside assembly caption is not a second exterior port.
    # Independently bind its single accepted native pose and actual MK1 owner;
    # a changed label contract cannot bless a shifted/mirrored/wrong-face label.
    rf_owner_matches = (mic is not None
                        and mic.get("footprint") == "Leshy2:CMEJ-0413-42-SMT-TR"
                        and mic.get("value") == "Same Sky CMEJ-0413-42-SMT-TR"
                        and mic.get("side") == "B.Cu"
                        and near(mic["rotation_deg"] % 360, 0)
                        and len(mic["anchor_mm"]) == 2
                        and all(near(v, e) for v, e in zip(mic["anchor_mm"], [47., 147.4])))
    rf_label_matches = (isinstance(rf_mic_labels, list)
                        and (not rf_mic_labels or (len(rf_mic_labels) == 1
                             and rf_owner_matches and exact_microphone_label(
                                 rf_mic_labels[0], "B.Silkscreen", [46.75, 142.35], True, tol))))
    check("RF MIC is absent or the single exact inner assembly caption of actual MK1",
          rf_label_matches,
          {"rf_labels": rf_mic_labels, "actual_owner": mic,
           "expected_owner": {"reference": "MK1", "side": "B.Cu",
                              "anchor_mm": [47., 147.4], "rotation_deg": 0},
           "expected_label": {"text": "MIC", "layer": "B.Silkscreen", "at_mm": [46.75, 142.35]},
           "role": "optional_inner_assembly", "replaces_required_UI_front_label": False})
    exterior_functions = {"BT1", "R33", "R34", "SW3", "SW4", "J5", "J6", "J7", "J8", "J9", "J10", "L32"}
    unexplained = sorted(ref for ref, row in rf.items()
                         if row["side"] == "F.Cu" and ref not in exterior_functions
                         and not ref.startswith("MH"))
    check("no ordinary RF support components moved outside merely to solve packing",
          not unexplained, unexplained)
    # Independently require the exact four approved ports, not a mutable count
    # or the old JAE mouth datum. A missing port must fail rather than disappear.
    usb_rows = []
    for board, ref, x in ((rf, "J1", 16.47), (rf, "J4", 37.47),
                          (ui, "J9", 26.1), (ui, "J11", 14.87)):
        usb = board.get(ref, {})
        anchor = usb.get("anchor_mm", [])
        good = (usb.get("footprint") == "Connector_USB:USB_C_Receptacle_GCT_USB4105-xx-A_16P_TopMnt_Horizontal"
                and usb.get("value") == "GCT USB4105-GF-A" and usb.get("side") == "B.Cu"
                and near(usb.get("rotation_deg", 0) % 360, 180) and len(anchor) == 2
                and near(anchor[0], x) and near(anchor[1], 146.325)
                and near(anchor[1] + 3.675, height))
        usb_rows.append({"reference": ref, "pose": usb, "pass": good,
                         "nominal_mouth_y_mm": anchor[1]+3.675 if len(anchor) == 2 else None})
    check("four exact GCT USB ports inside the sandwich with uniform nominal flush mouths",
          len(usb_rows) == 4 and all(row["pass"] for row in usb_rows), usb_rows)
    sd = ui["J5"]
    notch = checked_native_notch(snapshot.get("bottom_edges", {}).get(PROJECTS[0], []))
    check("actual native microSD notch is open at the reviewed bottom-edge datum",
          notch["pass"], notch)
    locked, pushed, ejected = [sd["anchor_mm"][1]+v for v in (9.725, 8.925, 13.725)]
    card_axis = sd["anchor_mm"][0] + .425
    check("microSD locked card recessed; pressed card remains accessible at notch",
          sd["side"] == "B.Cu" and near(sd["rotation_deg"] % 360, 180)
          and notch["pass"] and near(card_axis, notch["axis_x_mm"])
          and notch["floor_y_mm"] < pushed < locked < height < ejected,
          {"card_axis_x_mm": card_axis, "notch_axis_x_mm": notch.get("axis_x_mm"),
           "locked_y_mm": locked, "pushed_y_mm": pushed, "ejected_y_mm": ejected})
    for left, right in zip(range(9, 13), range(13, 17)):
        a, b = ui[f"SW{left}"], ui[f"SW{right}"]
        ax, bx = a["actuator_mm"], b["actuator_mm"]
        check(f"F{left-8}/F{right-8} equal physical actuator edge insets",
              ax is not None and bx is not None and a["side"] == b["side"] == "F.Cu"
              and near(ax[0], width-bx[0]) and near(ax[1], bx[1]), [ax, bx])
    for project, refs in ((PROJECTS[0], ("J12", "J3", "J14", "J7", "J16")),
                          (PROJECTS[1], ("J9", "J8", "J5", "J6", "J7"))):
        bank = [snapshot["boards"][project][r] for r in refs]
        xs = [r["anchor_mm"][0] for r in bank]
        pitches = [b-a for a, b in zip(xs, xs[1:])]
        check(f"{project} five symmetric outward SMA ports at >=14.7mm pitch",
              all(r["side"] == "F.Cu" and near(r["anchor_mm"][1], 0)
                  and near(r["rotation_deg"] % 360, 180) for r in bank)
              and all(p >= 14.7-tol for p in pitches)
              and max(pitches)-min(pitches) < tol and near(xs[0]+xs[-1], width), xs)
    check("RF antenna labels match the actual UHF/VHF signal identities",
          rf["J6"]["pad1_nets"] == ["/RF_20_CC1101_VOICE_TX/VOICE_U_EXTERNAL_RF_50R"]
          and rf["J7"]["pad1_nets"] == ["/RF_20_CC1101_VOICE_TX/VOICE_V_EXTERNAL_RF_50R"],
          {r: rf[r]["pad1_nets"] for r in ("J6", "J7")})
    return {"schema_version": 1, "status": "pass" if all(c["pass"] for c in checks) else "fail",
            "scope": "Independent planar product intent from native PCB; not general DRC or assembled-Z qualification",
            "sources": snapshot.get("sources", {}), "checks": checks,
            "failed_requirements": [c["requirement"] for c in checks if not c["pass"]]}


def main():
    parser = argparse.ArgumentParser(description=__doc__)
    parser.add_argument("--write", action="store_true")
    parser.add_argument("--check", action="store_true")
    args = parser.parse_args()
    result = evaluate(native_snapshot())
    content = json.dumps(result, indent=2, ensure_ascii=False) + "\n"
    if args.write:
        DEST.write_text(content)
    if args.check and (not DEST.exists() or DEST.read_text() != content):
        raise SystemExit("placement-intent report is stale")
    print(json.dumps({"status": result["status"], "failed": result["failed_requirements"]}, ensure_ascii=False))
    return 0 if result["status"] == "pass" else 1


if __name__ == "__main__":
    raise SystemExit(main())
