anton-vinogradov/esp32-leshy2/hardware/ecad/h2_r2_native_kicad.py

#!/usr/bin/env python3
"""Generate the two current H2-R2 native KiCad schematic projects.

The generator deliberately stops at logical schematics.  It materializes the
reviewed fitted-instance ledger, exact controlled symbols, canonical networks
and explicit no-connects, but creates no PCB, placement, routing or production
files.  R1 KiCad projects are never read by this generator.
"""

from __future__ import annotations

import argparse
import hashlib
import json
import re
import uuid
from collections import defaultdict
from pathlib import Path


ROOT = Path(__file__).resolve().parents[2]
CONTRACT_PATH = ROOT / "hardware/ecad/h2-r2-native-kicad-contract.json"
UUID_NAMESPACE = uuid.UUID("55d78bc6-bb67-4c34-aa29-29952908dcf4")
# These two canonical GPIO identities are the USB/SDIO switch's shared side.
# Preserve the canonical contract while exposing one native USB routing pair.
USB_SHARED_NATIVE_ALIASES = {
    "C5_GPIO13_COMMON": "C5_USB_SDIO_COMMON_N",
    "C5_GPIO14_COMMON": "C5_USB_SDIO_COMMON_P",
}


def load(path: Path) -> dict:
    return json.loads(path.read_text(encoding="utf-8"))


def sha256_bytes(value: bytes) -> str:
    return hashlib.sha256(value).hexdigest()


def sha256(path: Path) -> str:
    return sha256_bytes(path.read_bytes())


def stable_uuid(scope: str) -> str:
    return str(uuid.uuid5(UUID_NAMESPACE, scope))


def escaped(value: object) -> str:
    return str(value).replace("\\", "\\\\").replace('"', '\\"')


def kicad_net_name(canonical: str) -> str:
    """Give USB pairs a terminal P/N suffix understood by KiCad's router.

    The reviewed cross-domain contract keeps the conventional DP/DM spelling.
    KiCad, however, discovers differential pairs only from a common basename
    followed by P/N (or +/-).  Move the polarity marker to the physical label's
    final suffix without changing the canonical net identity. The exact C5
    shared-side aliases also retain their SDIO function in the native basename.
    """
    if canonical in USB_SHARED_NATIVE_ALIASES:
        return USB_SHARED_NATIVE_ALIASES[canonical]
    match = re.match(r"^(.*(?:USB2|USB))_D([PM])(.*)$", canonical)
    if not match:
        return canonical
    polarity = "P" if match.group(2) == "P" else "N"
    return f"{match.group(1)}{match.group(3)}_{polarity}"


def natural_key(value: str) -> tuple:
    return tuple(int(part) if part.isdigit() else part for part in re.split(r"(\d+)", value))


def effects(justify: str | None = None, size: float = 1.27) -> str:
    suffix = f" (justify {justify})" if justify else ""
    return f"(effects (font (size {size:.2f} {size:.2f})){suffix})"


def property_block(
    key: str,
    value: object,
    x: float,
    y: float,
    *,
    hide: bool = False,
) -> list[str]:
    lines = [
        f'\t\t(property "{escaped(key)}" "{escaped(value)}"',
        f"\t\t\t(at {x:.2f} {y:.2f} 0)",
        "\t\t\t(show_name no)",
        "\t\t\t(do_not_autoplace no)",
    ]
    if hide:
        lines.append("\t\t\t(hide yes)")
    lines += [f"\t\t\t{effects()}", "\t\t)"]
    return lines


def parenthesis_delta(line: str) -> int:
    """Count structural parentheses while ignoring quoted strings."""
    delta = 0
    quoted = False
    escaped_char = False
    for char in line:
        if escaped_char:
            escaped_char = False
            continue
        if char == "\\" and quoted:
            escaped_char = True
            continue
        if char == '"':
            quoted = not quoted
        elif not quoted and char == "(":
            delta += 1
        elif not quoted and char == ")":
            delta -= 1
    return delta


def embedded_symbol_definitions(library_text: str) -> dict[str, str]:
    """Extract top-level controlled symbols and namespace them for schematics."""
    definitions: dict[str, str] = {}
    lines = library_text.splitlines()
    index = 0
    while index < len(lines):
        match = re.match(r'^\t\(symbol "([^"]+)"$', lines[index])
        if not match:
            index += 1
            continue
        device_id = match.group(1)
        block = [lines[index]]
        depth = parenthesis_delta(lines[index])
        index += 1
        while depth and index < len(lines):
            block.append(lines[index])
            depth += parenthesis_delta(lines[index])
            index += 1
        if depth:
            raise ValueError(f"unterminated controlled symbol: {device_id}")
        block[0] = block[0].replace(
            f'\t(symbol "{device_id}"',
            f'\t(symbol "Leshy2_R2:{device_id}"',
            1,
        )
        definitions[device_id] = "\n".join("\t" + line for line in block)
    return definitions


def pin_layout(symbol: dict) -> tuple[dict[str, tuple[float, float, str]], float]:
    pins = symbol["pin_map"]
    midpoint = (len(pins) + 1) // 2
    left, right = pins[:midpoint], pins[midpoint:]
    rows = max(len(left), len(right), 2)
    top = (rows - 1) * 1.27
    result: dict[str, tuple[float, float, str]] = {}
    for side, side_pins in (("left", left), ("right", right)):
        for index, pin in enumerate(side_pins):
            x = -20.32 if side == "left" else 20.32
            result[pin["number"]] = (x, top - index * 2.54, side)
    return result, max(10.16, rows * 2.54)
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
