anton-vinogradov/esp32-leshy2/hardware/architecture/h0_r2_report.py

#!/usr/bin/env python3
"""Generate the public H0-R2 architecture report and compact visual evidence."""

from __future__ import annotations

import csv
import html
import json
from pathlib import Path


ROOT = Path(__file__).resolve().parents[2]
SOURCE = ROOT / "hardware/architecture/h0-r2-rebaseline.json"
REPORT_EN = ROOT / "docs/h0-r2-functional-architecture.md"
REPORT_RU = ROOT / "docs/h0-r2-functional-architecture.ru.md"
SVG = ROOT / "docs/images/h0-r2-functional-architecture.svg"
BOM = ROOT / "hardware/architecture/generated/H0-R2-airband-bom-delta.csv"


def load() -> dict:
    return json.loads(SOURCE.read_text(encoding="utf-8"))


def render_svg_legacy(data: dict) -> str:
    air = data["airband_contract"]
    hub = data["hub_rp"]["gpio_budget"]
    blocks = [
        ("FM / SW / AIR RX", "existing standard-SMA port", "#eff6ff", "#2563eb"),
        ("118–137 MHz BPF", "serial LC · BPF-A127+ mask", "#ecfdf5", "#059669"),
        ("PGA-103+", "C3008207 · low-noise gain", "#ecfdf5", "#059669"),
        ("LT5560EDD#TRPBF", "C462645 · RF − 112 MHz", "#fff7ed", "#ea580c"),
        ("HMC544AETR", "C579555 · direct / converted", "#f5f3ff", "#7c3aed"),
        ("SI4732-A10-GSR", "C2155558 · 6–25 MHz FMI", "#eff6ff", "#2563eb"),
        ("SC1512-A4 · Hub RP", "I²C control · audio · recording", "#f8fafc", "#334155"),
        ("ESP32-S3-WROOM-1U-N16R8", "UI and direct display stay local", "#eff6ff", "#2563eb"),
    ]
    width = 760
    box_x, box_w, box_h, gap = 145, 470, 58, 25
    height = 130 + len(blocks) * (box_h + gap) + 115
    out = [
        f'<svg xmlns="http://www.w3.org/2000/svg" width="{width}" height="{height}" viewBox="0 0 {width} {height}">',
        '<defs><marker id="a" markerWidth="8" markerHeight="8" refX="7" refY="3" orient="auto"><path d="M0,0 L7,3 L0,6 Z" fill="#475569"/></marker></defs>',
        '<rect width="100%" height="100%" fill="#ffffff"/>',
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
